yangit/flactyl/photos/1.jpeg

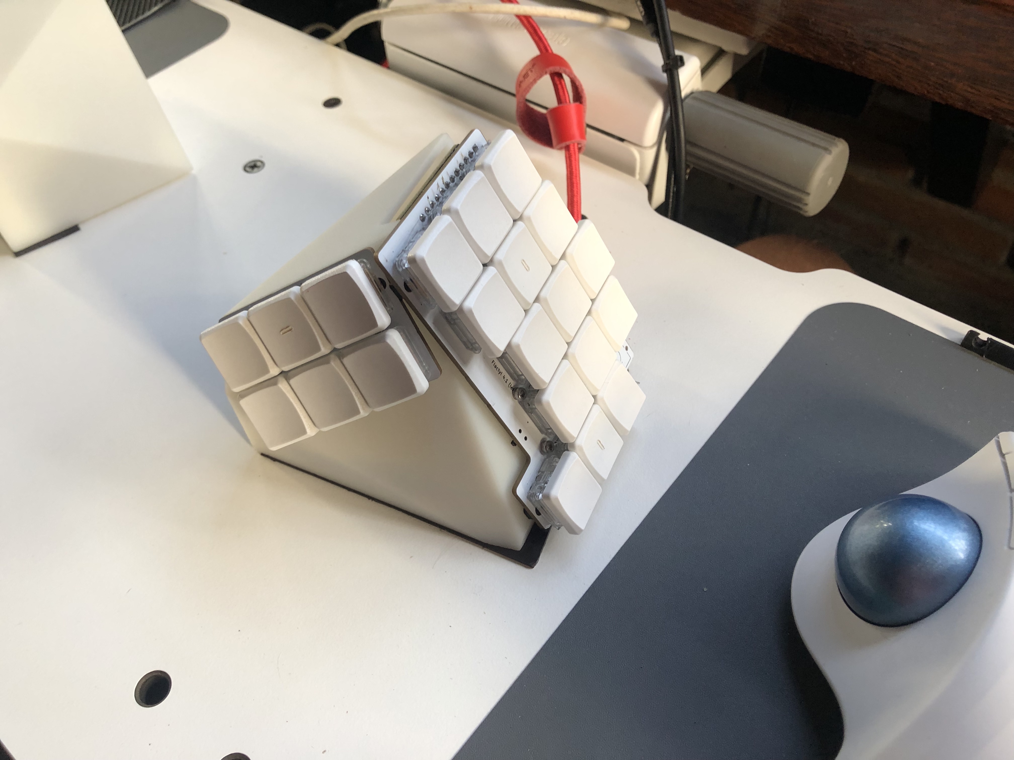
photos/1.jpeg
