yangit/flactyl/photos/4.jpeg

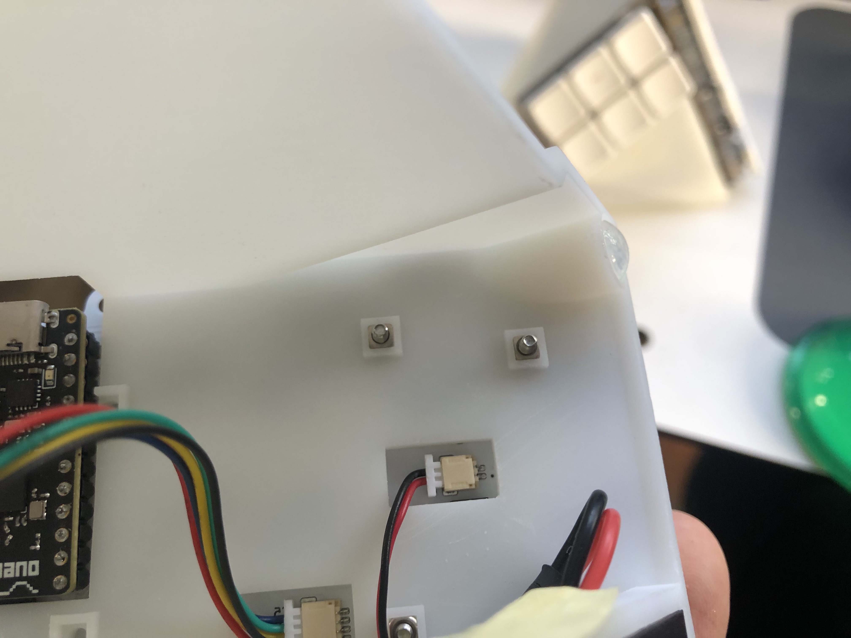
photos/4.jpeg
