yangit/flactyl/photos/6.jpeg

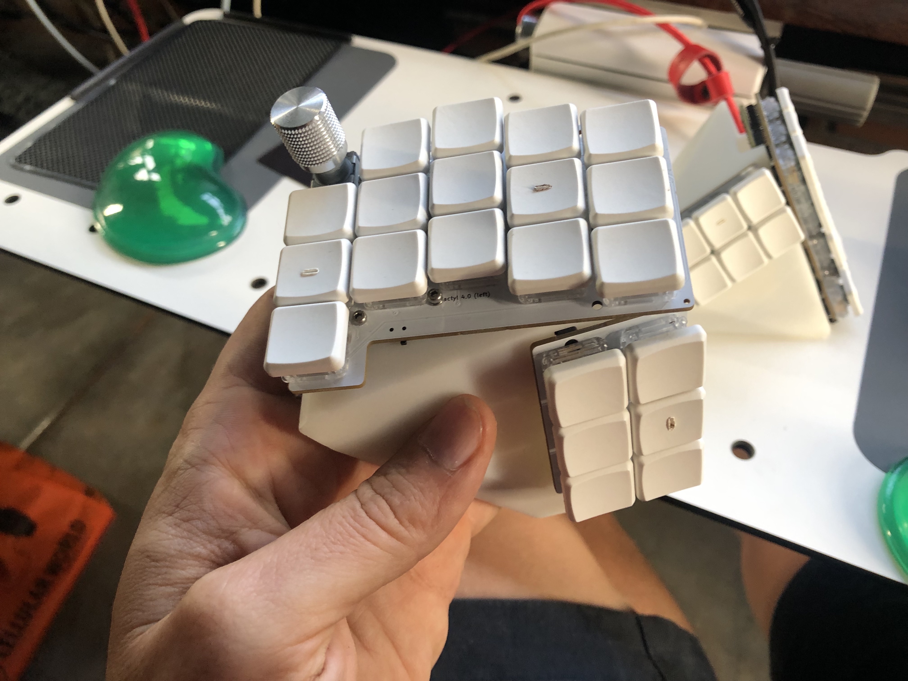
photos/6.jpeg
