yangit/flactyl/photos/7.jpeg

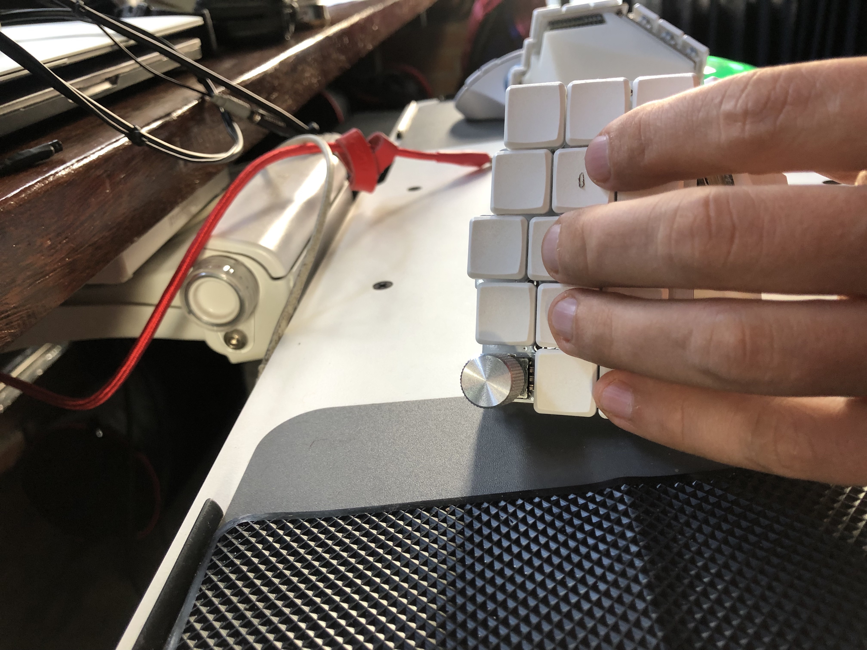
photos/7.jpeg
