yangit/flactyl/photos/8.jpeg

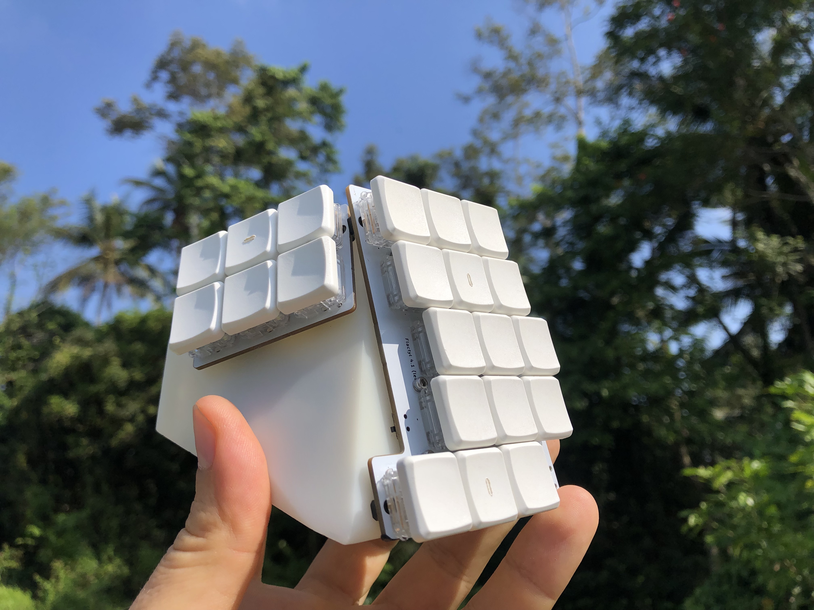
photos/8.jpeg
