yangit/flactyl/photos/9.jpeg

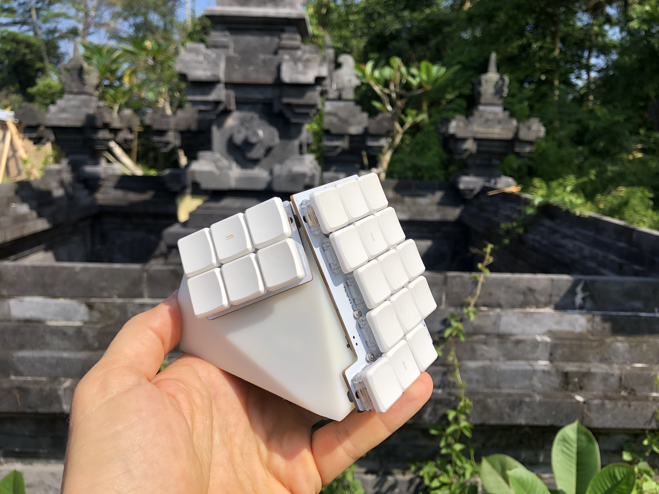
photos/9.jpeg
