yangit/flactyl/photos/10.jpeg

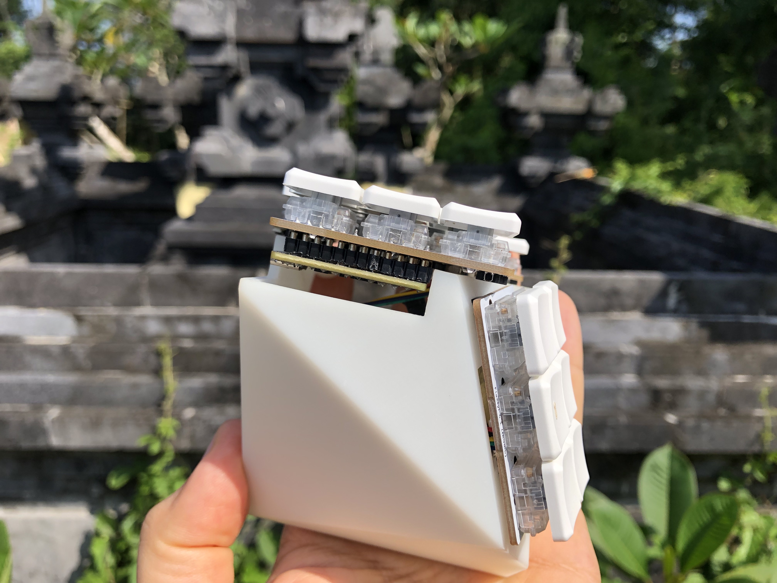
photos/10.jpeg
