yangit/flactyl/photos/11.jpeg

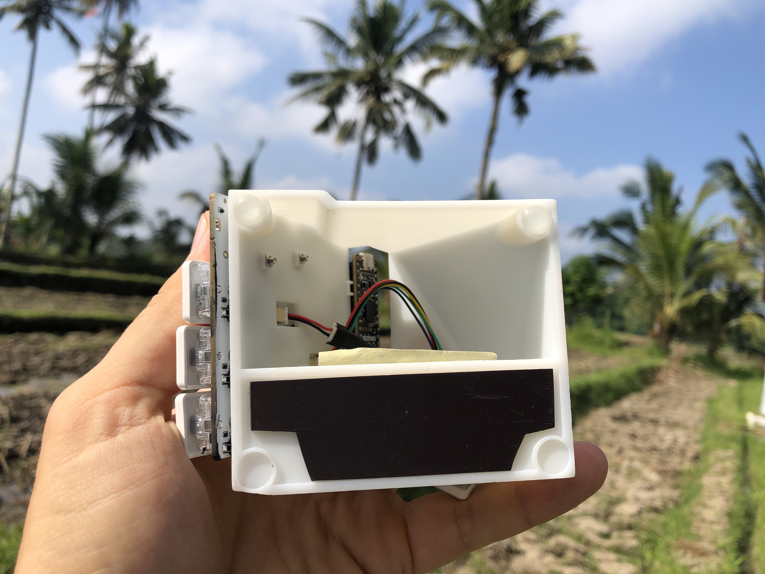
photos/11.jpeg
