yangit/flactyl/photos/12.jpeg

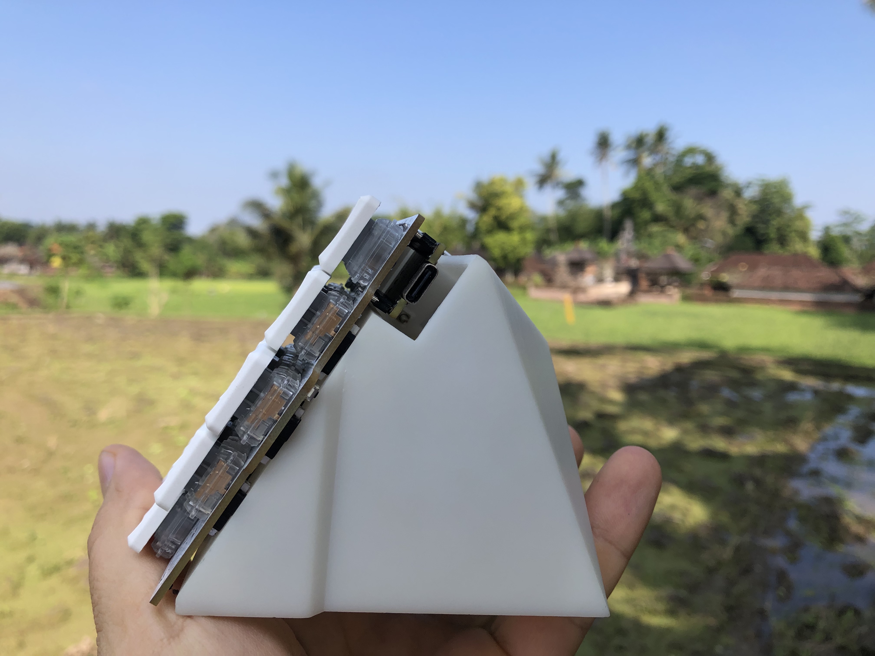
photos/12.jpeg
