yangit/flactyl/photos/cases/hitam1.png

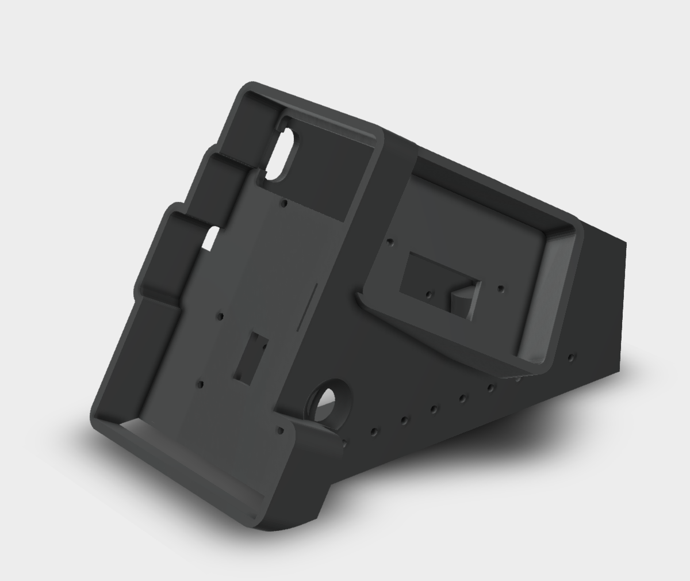
photos/cases/hitam1.png
