yangit/flactyl/photos/cases/hitam2.png

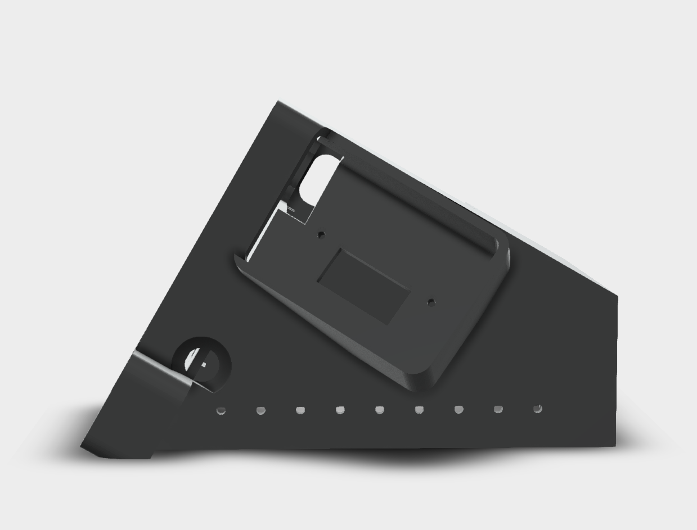
photos/cases/hitam2.png
