yangit/flactyl/production/case/4.2/iceberg/variant0/case4.png

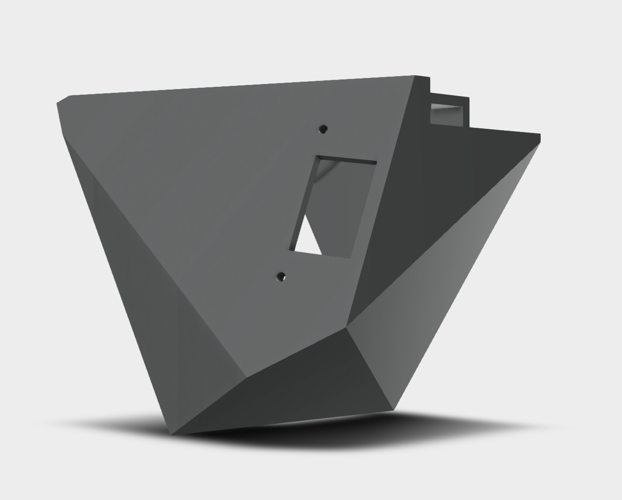
production/case/4.2/iceberg/variant0/case4.png
