yangit/flactyl/scad/4.2/clay/thumb.png

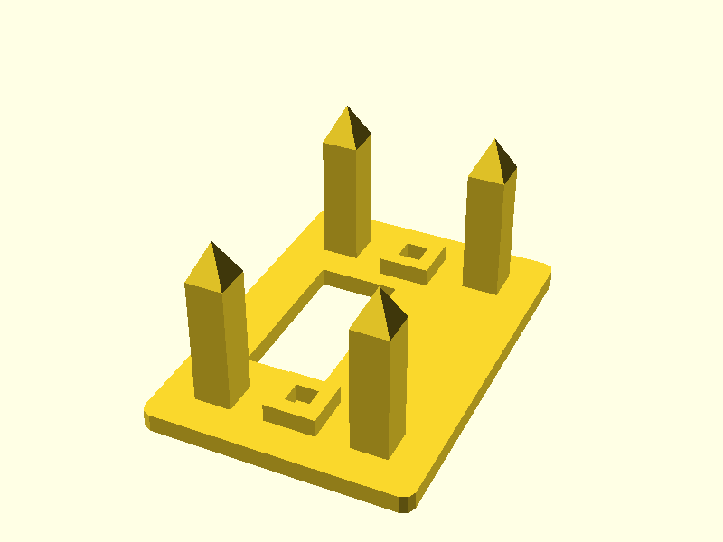
scad/4.2/clay/thumb.png
