yangit/flactyl/photos/parts/nut.webp

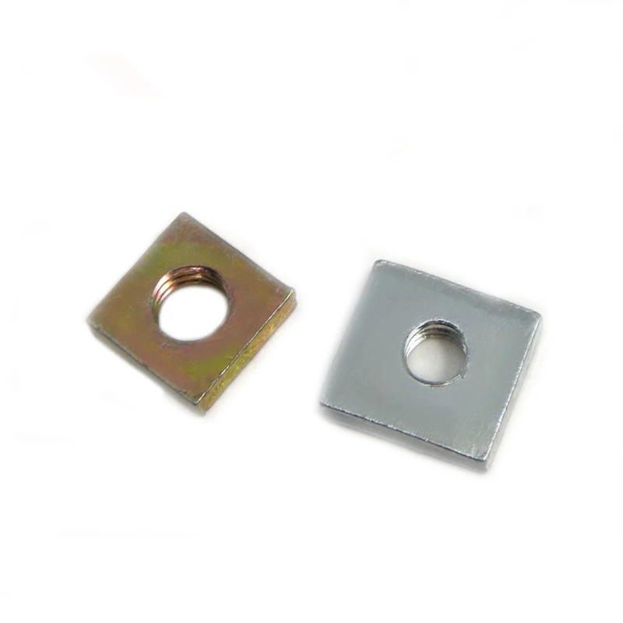
photos/parts/nut.webp
