yangit/flactyl/photos/parts/nut_how.jpg

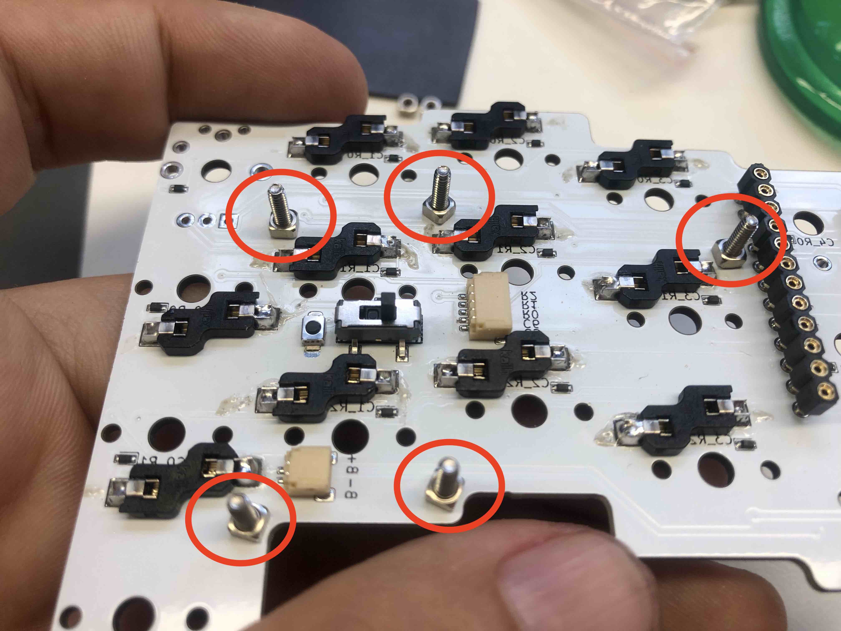
photos/parts/nut_how.jpg
