yangit/flactyl/production/case/iceberg/left2.stl

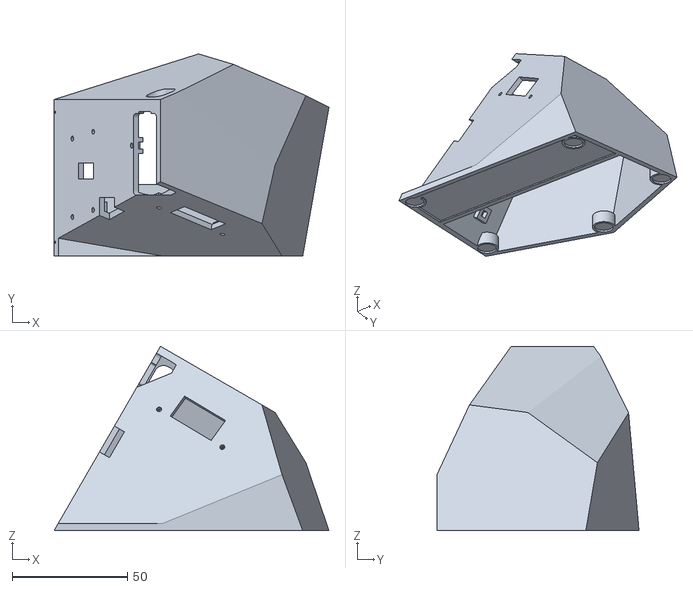
[picture p83: CAD file, 2023-06-13]
production/case/iceberg/left2.stl
119.5 x 87.8 x 80.1
