yangit/flactyl/production/manual_3d_print/batch0/case3 v20.stl

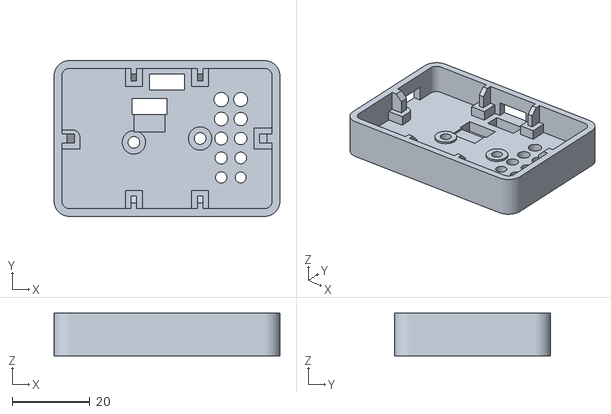
[picture p84: CAD file, 2023-05-24]
production/manual_3d_print/batch0/case3 v20.stl
58.0 x 40.0 x 11.0
