yangit/flactyl/production/manual_3d_print/batch1/switch_cutout_005.stl

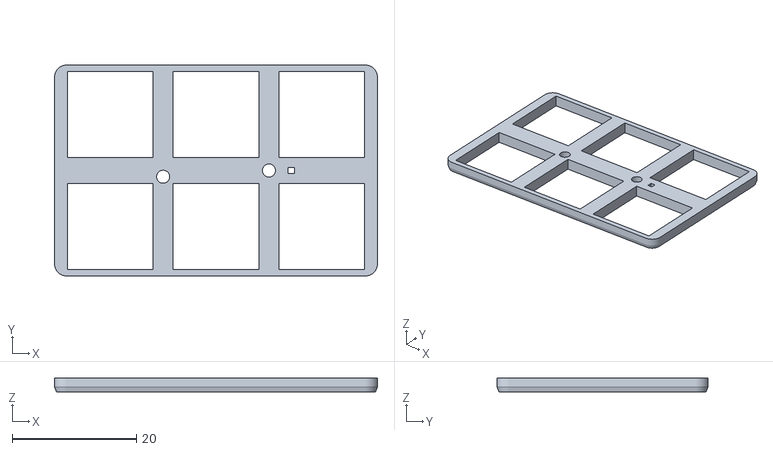
[picture p85: CAD file, 2023-05-24]
production/manual_3d_print/batch1/switch_cutout_005.stl
51.9 x 33.9 x 2.20
