yangit/flactyl/production/manual_3d_print/batch2/srcew-mount-bike.stl

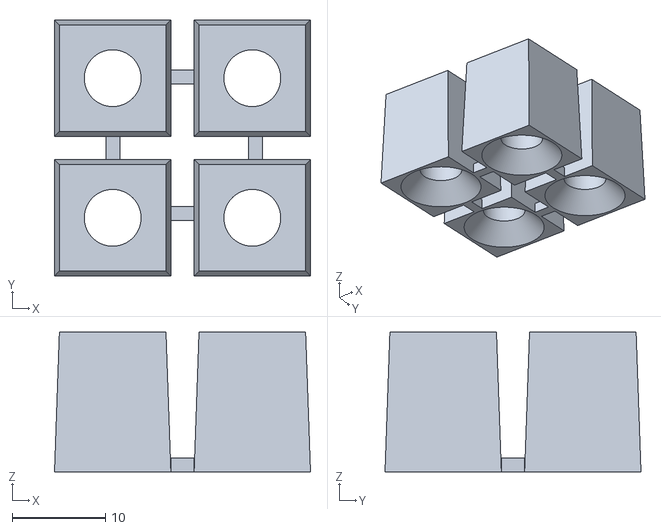
[picture p86: CAD file, 2023-05-24]
production/manual_3d_print/batch2/srcew-mount-bike.stl
27.5 x 27.5 x 15.0
