yangit/flactyl/production/manual_3d_print/batch3/left_3.2.stl

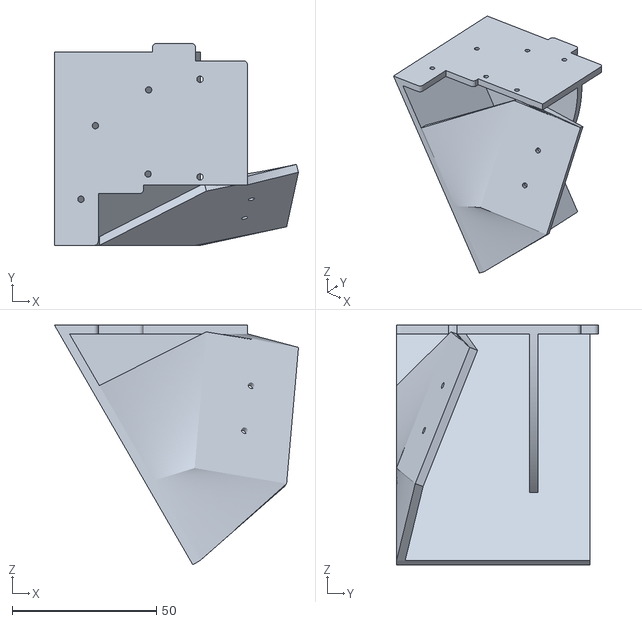
[picture p87: CAD file, 2023-05-24]
production/manual_3d_print/batch3/left_3.2.stl
84.6 x 70.0 x 83.0
