yangit/flactyl/production/pcbs/5.0/left/left.step

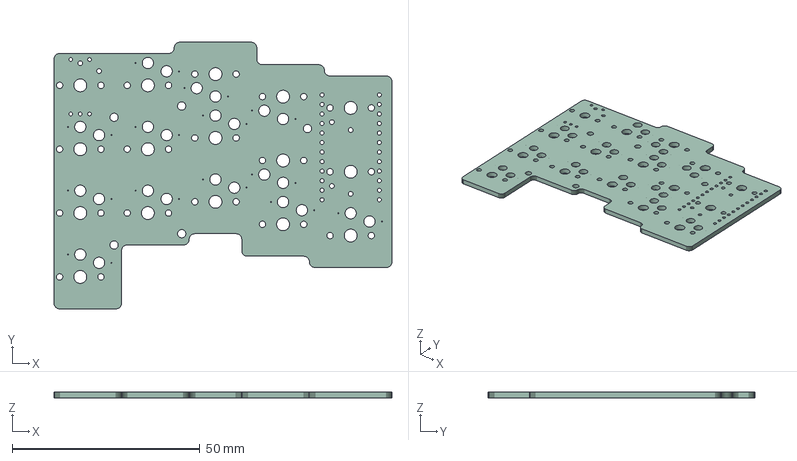
[picture p88: CAD file, 2023-06-15]
production/pcbs/5.0/left/left.step
90.0 x 71.0 x 1.60 mm
