yangit/flactyl/production/pcbs/5.0/thumb3/thumb3.step

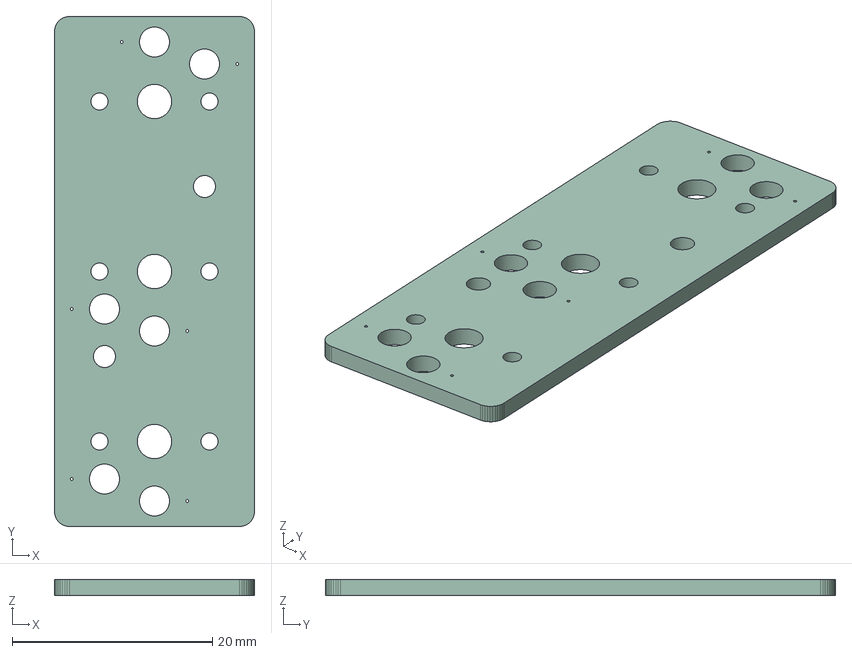
[picture p89: CAD file, 2023-06-29]
production/pcbs/5.0/thumb3/thumb3.step
20.0 x 51.0 x 1.60 mm
