yangit/flactyl/production/pcbs/5.1/test/test.step

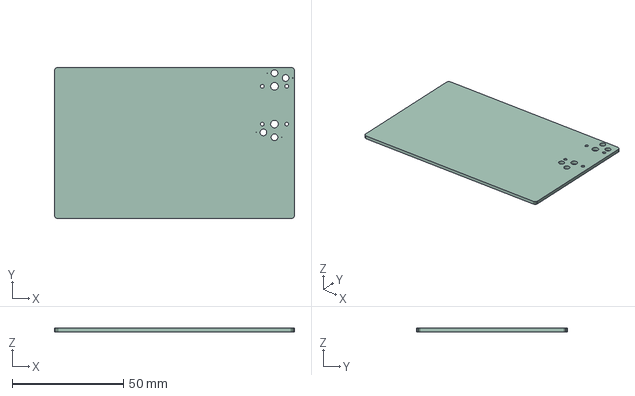
[picture p90: CAD file, 2023-08-01]
production/pcbs/5.1/test/test.step
108.0 x 68.0 x 1.60 mm
