yangit/flactyl/production/pcbs/5.1/thumb/thumb.step

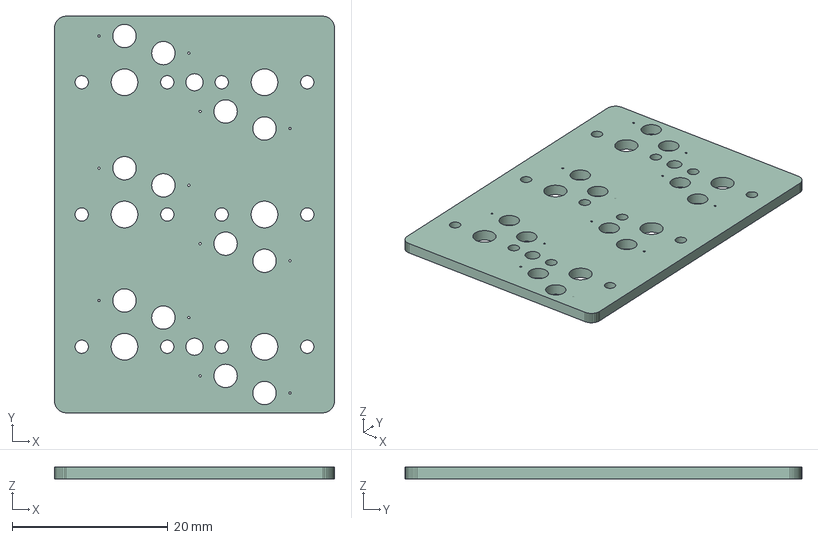
[picture p91: CAD file, 2023-08-01]
production/pcbs/5.1/thumb/thumb.step
36.0 x 51.0 x 1.60 mm
