yangit/flactyl/scad/4.2/shared-3d-models/nice-nano.step

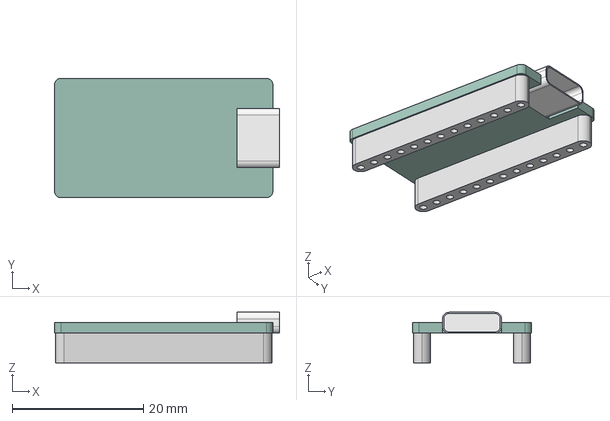
[picture p92: CAD file, 2023-06-29]
scad/4.2/shared-3d-models/nice-nano.step
34.3 x 18.2 x 7.70 mm
