yangit/flactyl/scad/5.0/shared-3d-models/pg1350_socket.3mf

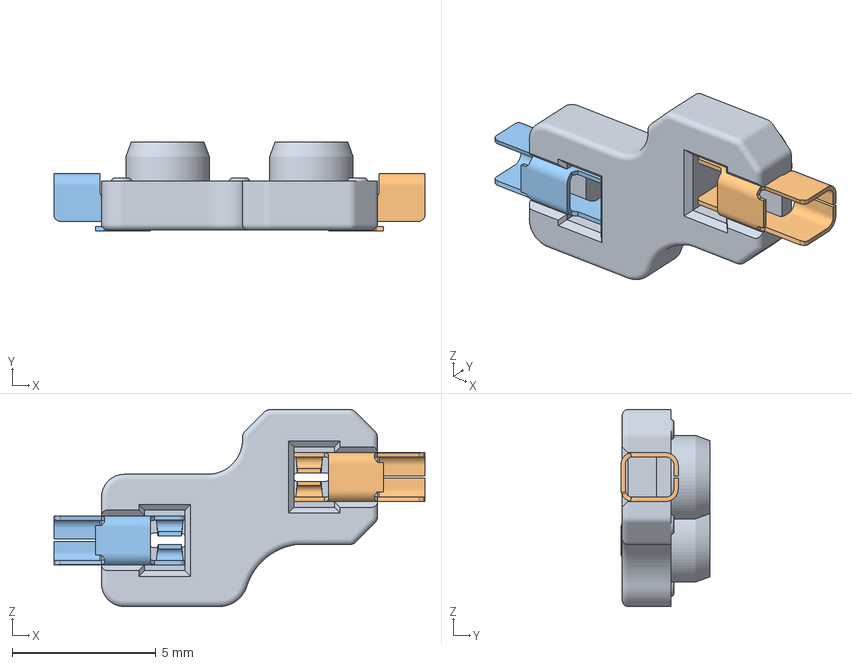
[picture p93: CAD file, 2023-07-01]
scad/5.0/shared-3d-models/pg1350_socket.3mf
12.9 x 3.09 x 6.85 mm
