yangit/flactyl/scad/5.0/shared-3d-models/ploopy-nano/STEPs/RollerBearingDowel.stp

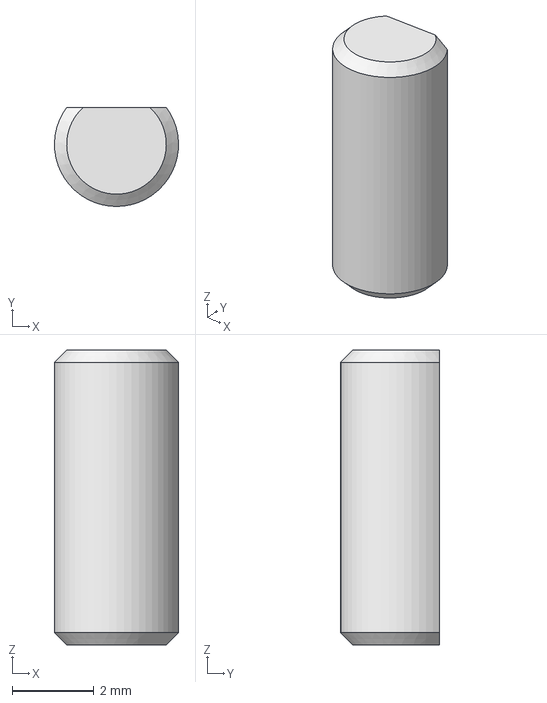
[picture p94: CAD file, 2023-06-29]
scad/5.0/shared-3d-models/ploopy-nano/STEPs/RollerBearingDowel.stp
3.03 x 2.42 x 7.20 mm
