yangit/flactyl/scad/5.0/shared-3d-models/ploopy-nano/STLs/Kit Bearing Press Bottom.stl

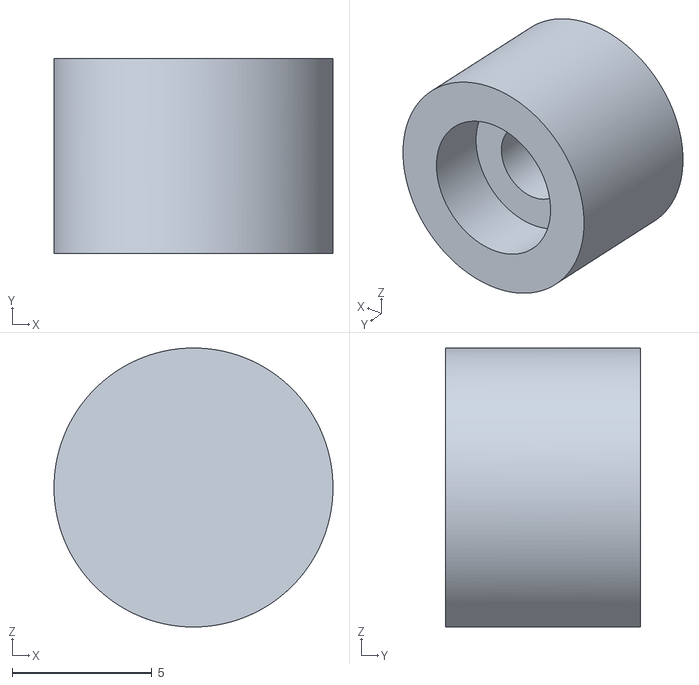
[picture p95: CAD file, 2023-06-29]
scad/5.0/shared-3d-models/ploopy-nano/STLs/Kit Bearing Press Bottom.stl
10.00 x 7.00 x 10.00
