yangit/flactyl/case/external_models/acrylic.dxf

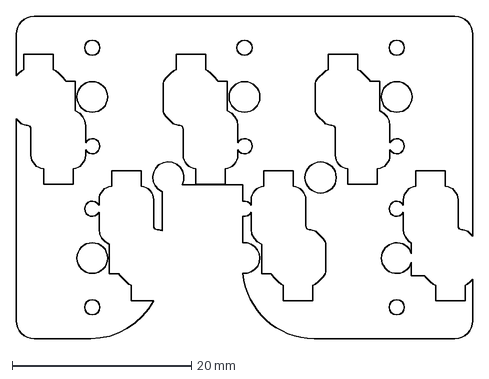
[picture p96: CAD file, 2023-05-24]
case/external_models/acrylic.dxf
51.0 x 36.0 mm
