yangit/flactyl/production/4.0/test/test.step

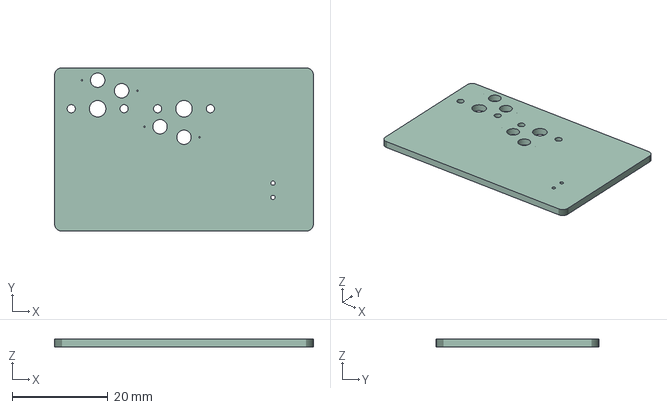
[picture p97: CAD file, 2023-06-08]
production/4.0/test/test.step
54.0 x 34.0 x 1.60 mm
