yangit/flactyl/production/4.1/right/right_keycaps.dxf

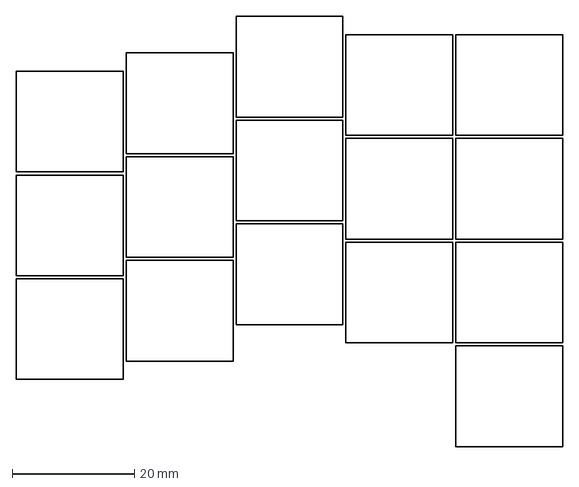
[picture p98: CAD file, 2023-06-08]
production/4.1/right/right_keycaps.dxf
89.5 x 70.5 mm
