yangit/flactyl/production/4.1/thumb/thumb_keycaps.dxf

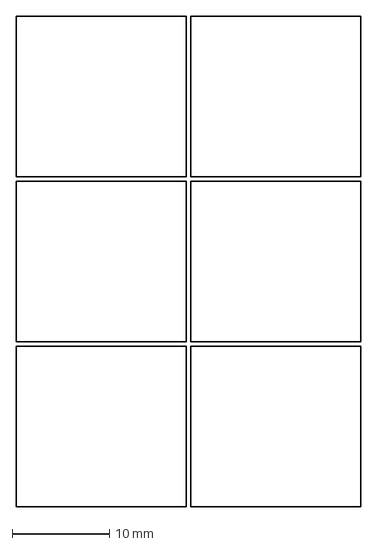
[picture p99: CAD file, 2023-06-08]
production/4.1/thumb/thumb_keycaps.dxf
35.5 x 50.5 mm
