yangit/flactyl/production/case/4.2/iceberg/variant0/right.stl

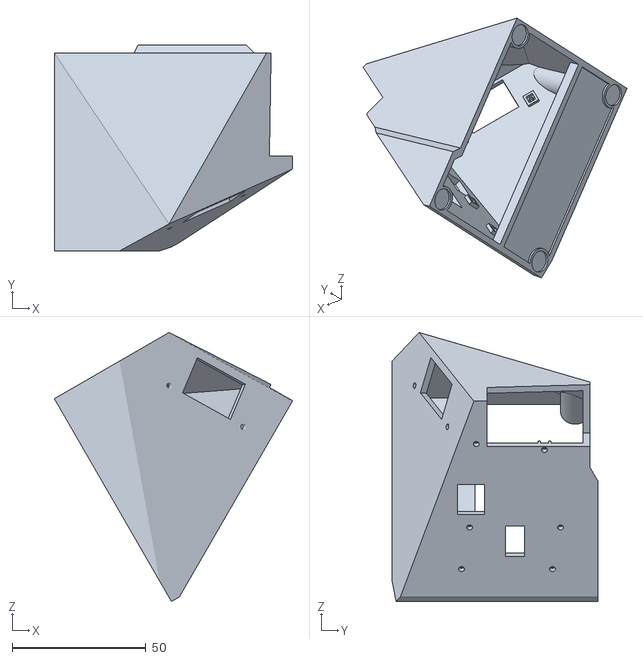
[picture p100: CAD file, 2023-05-24]
production/case/4.2/iceberg/variant0/right.stl
89.1 x 77.0 x 100.6
