yangit/flactyl/production/case/5.0/clay/thumb.stl

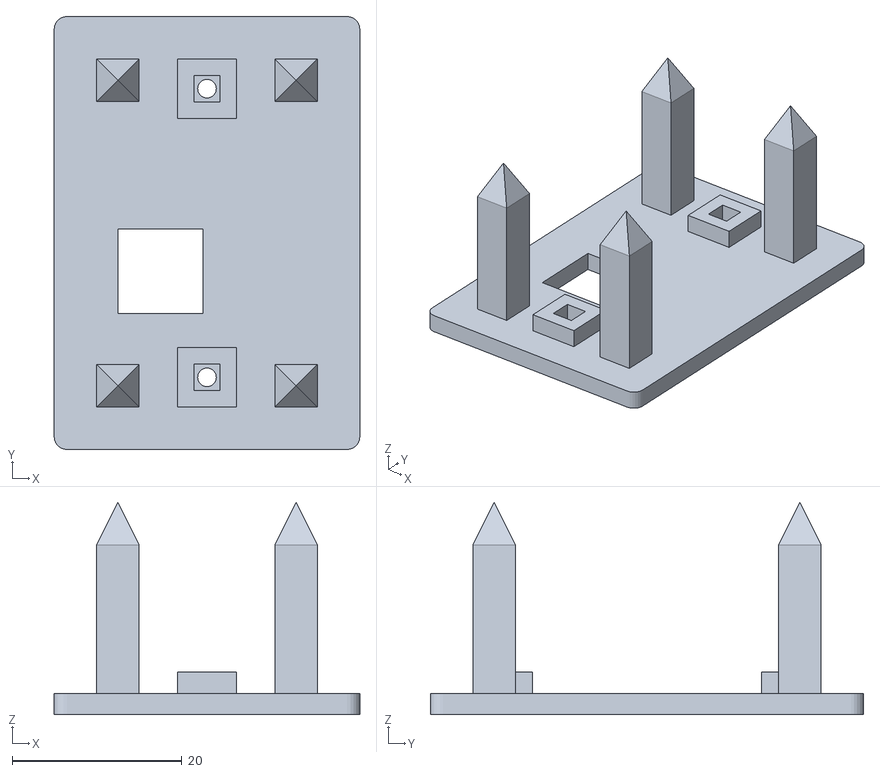
[picture p101: CAD file, 2023-07-02]
production/case/5.0/clay/thumb.stl
36.0 x 51.0 x 25.0
