yangit/flactyl/production/manual_3d_print/batch0/Holder v18_narrow.stl

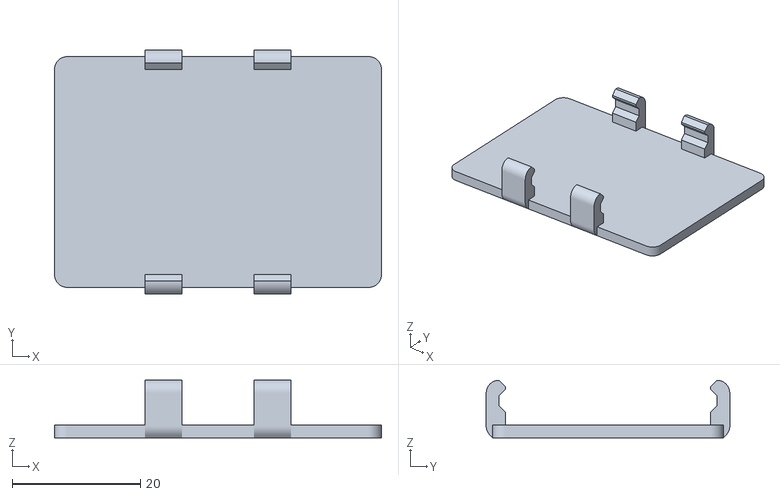
[picture p102: CAD file, 2023-05-24]
production/manual_3d_print/batch0/Holder v18_narrow.stl
51.0 x 38.0 x 8.97
