yangit/flactyl/production/manual_3d_print/batch1/switch_cutout_030.stl

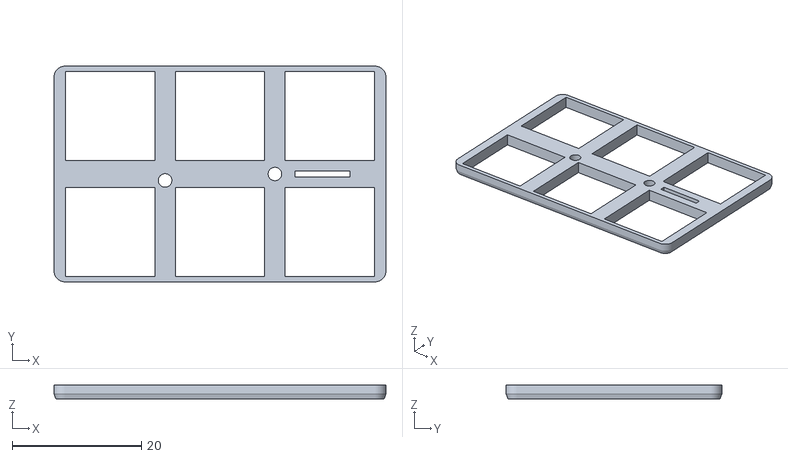
[picture p103: CAD file, 2023-05-24]
production/manual_3d_print/batch1/switch_cutout_030.stl
51.4 x 33.4 x 2.20
