yangit/flactyl/production/manual_3d_print/batch2/trainKaki.stl

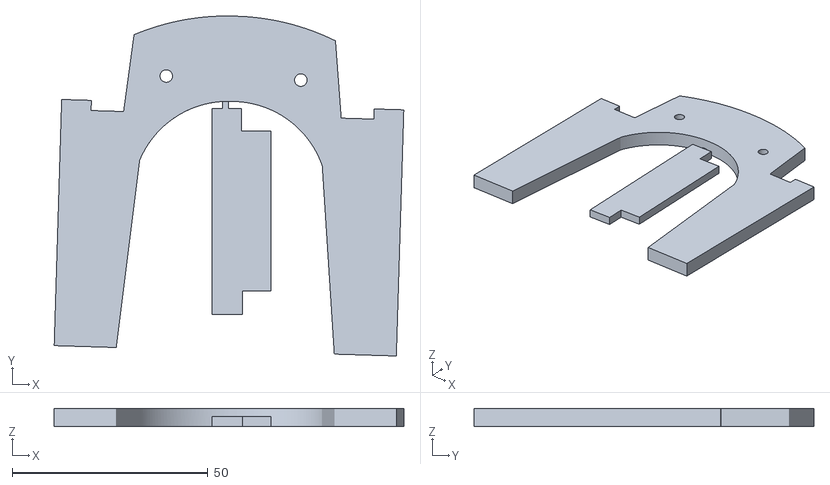
[picture p104: CAD file, 2023-05-24]
production/manual_3d_print/batch2/trainKaki.stl
89.3 x 86.8 x 4.60
