yangit/flactyl/production/manual_3d_print/batch3/right_3.2.stl

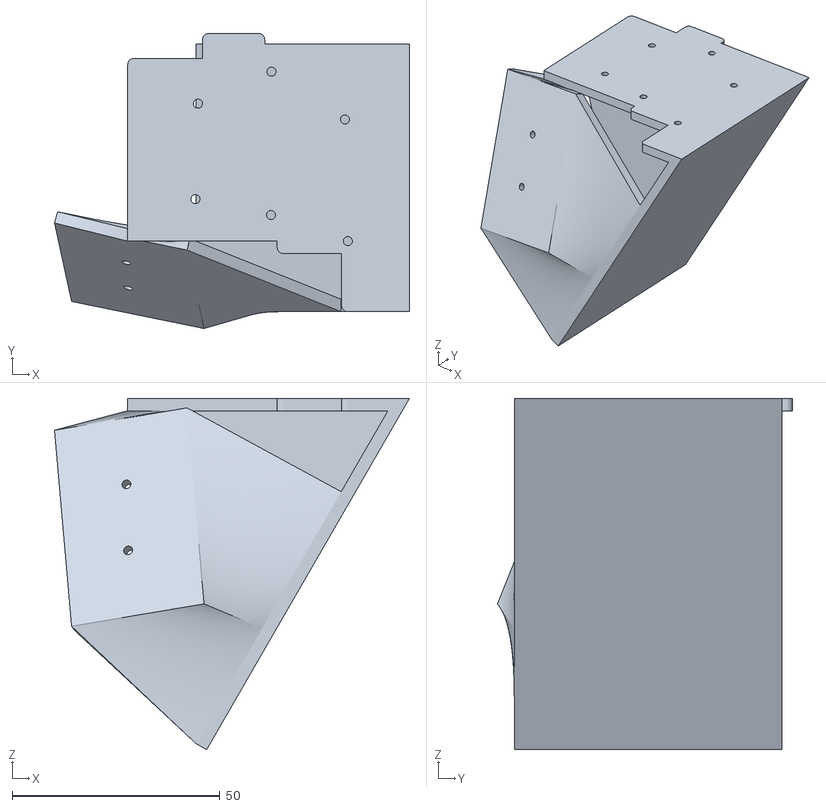
[picture p105: CAD file, 2023-05-24]
production/manual_3d_print/batch3/right_3.2.stl
85.5 x 71.0 x 84.6
