yangit/flactyl/production/pcbs/5.1/left/left_pcb_edgecut.dxf

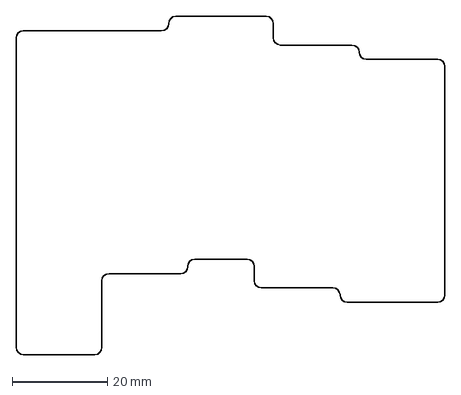
[picture p106: CAD file, 2023-06-15]
production/pcbs/5.1/left/left_pcb_edgecut.dxf
90.0 x 71.0 mm
