yangit/flactyl/production/pcbs/5.1/test/test_keycaps.dxf

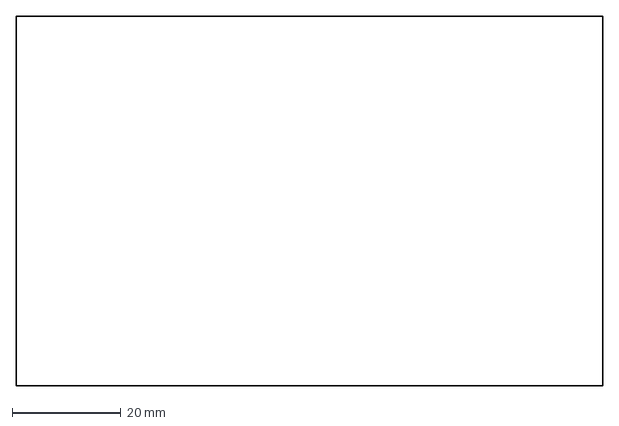
[picture p107: CAD file, 2023-06-08]
production/pcbs/5.1/test/test_keycaps.dxf
108.0 x 68.0 mm
