yangit/flactyl/production/pcbs/5.1/thumb/thumb_case.dxf

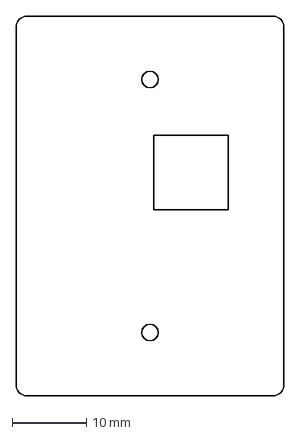
[picture p108: CAD file, 2023-08-01]
production/pcbs/5.1/thumb/thumb_case.dxf
36.0 x 51.0 mm
