yangit/flactyl/scad/4.2/shared-3d-models/choc-hot.stl

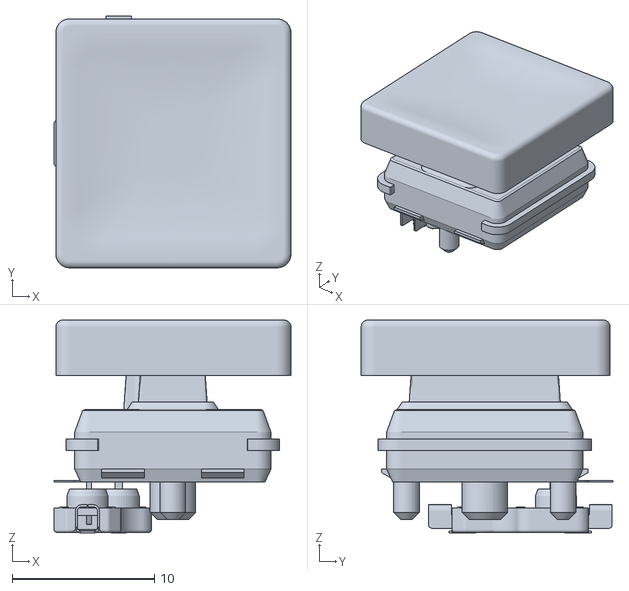
[picture p109: CAD file, 2023-06-01]
scad/4.2/shared-3d-models/choc-hot.stl
16.7 x 17.7 x 15.0
