yangit/flactyl/scad/5.0/shared-3d-models/ploopy-nano/STLs/Kit Bearing Press Top.stl

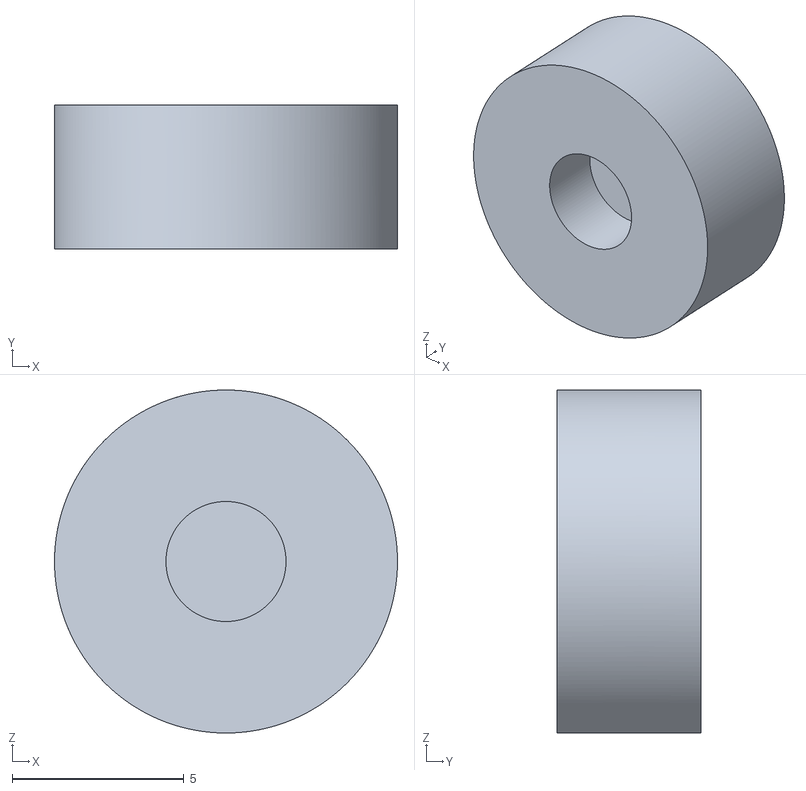
[picture p110: CAD file, 2023-06-29]
scad/5.0/shared-3d-models/ploopy-nano/STLs/Kit Bearing Press Top.stl
10.00 x 4.20 x 10.00
