yangit/flactyl/case/external_models/Kailh LP Choc PC Keycap.step

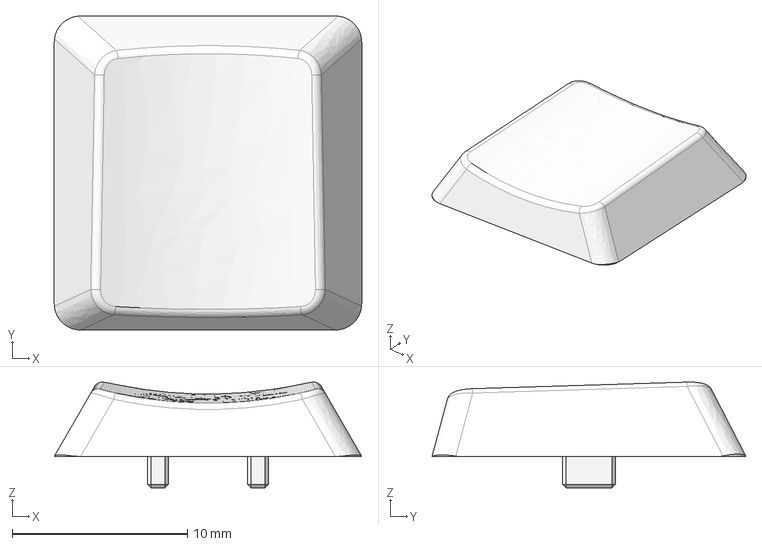
[picture p111: CAD file, 2023-05-24]
case/external_models/Kailh LP Choc PC Keycap.step
17.5 x 17.9 x 6.03 mm
