yangit/flactyl/production/4.0/test/test_pcb_edgecut.dxf

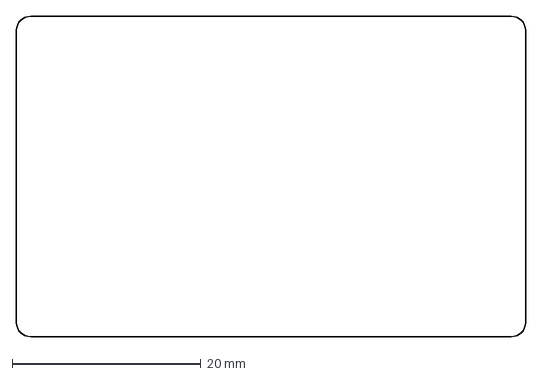
[picture p112: CAD file, 2023-06-08]
production/4.0/test/test_pcb_edgecut.dxf
54.0 x 34.0 mm
