yangit/flactyl/production/case/4.2/clay/thumb.stl

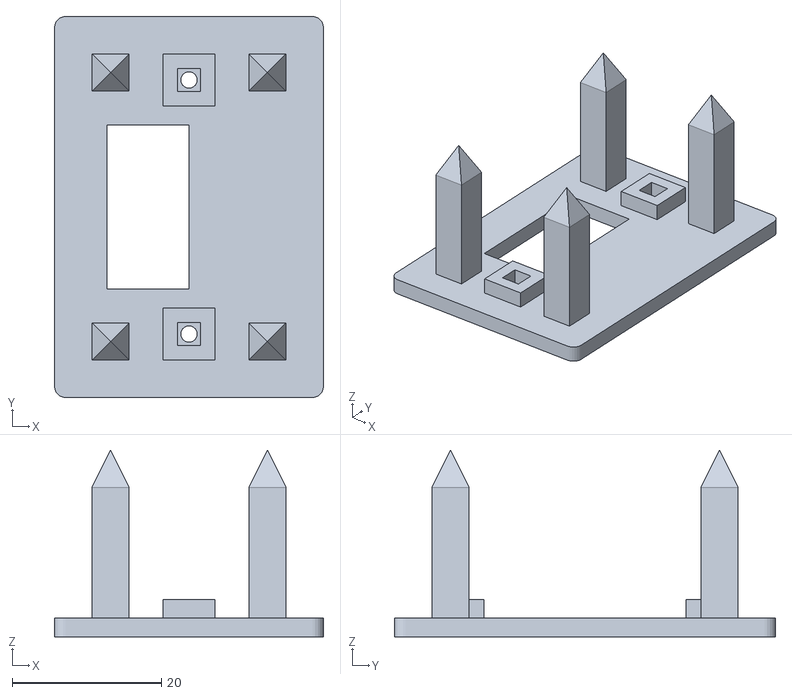
[picture p113: CAD file, 2023-06-13]
production/case/4.2/clay/thumb.stl
36.0 x 51.0 x 25.0
