yangit/flactyl/production/manual_3d_print/batch2/srcew-mount-bike-single.stl

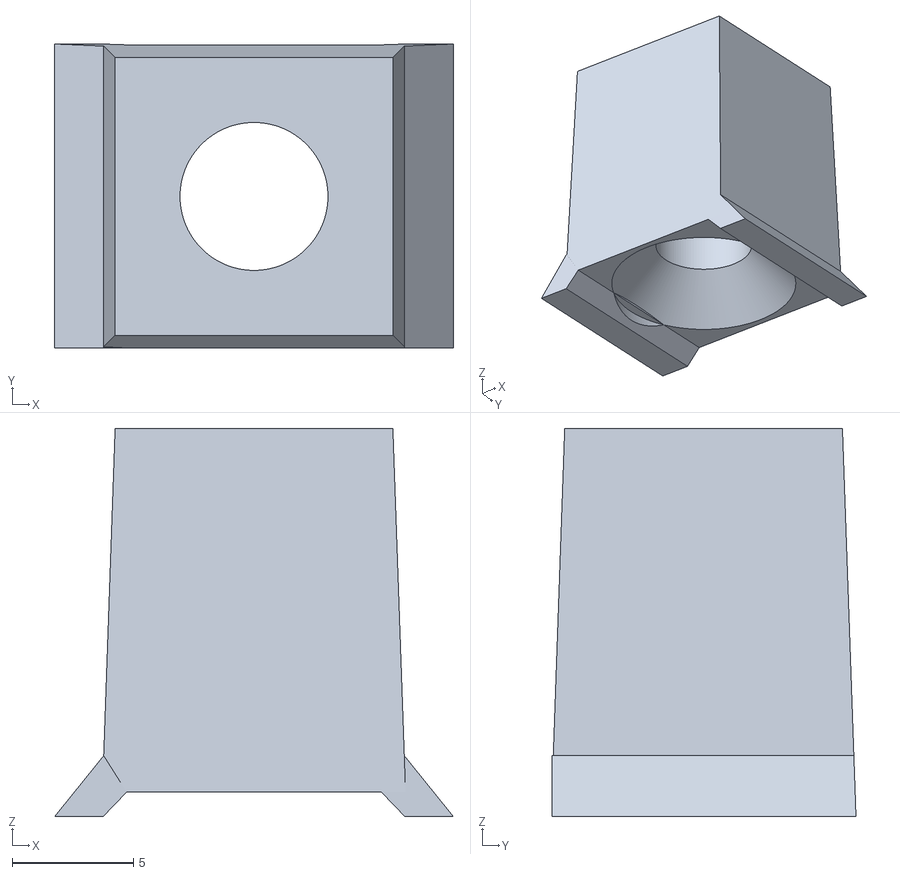
[picture p114: CAD file, 2023-05-24]
production/manual_3d_print/batch2/srcew-mount-bike-single.stl
16.5 x 12.5 x 16.0
