yangit/flactyl/production/pcbs/5.1/thumb3/thumb3_case.dxf

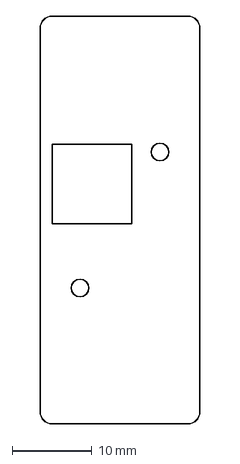
[picture p117: CAD file, 2023-06-29]
production/pcbs/5.1/thumb3/thumb3_case.dxf
20.0 x 51.0 mm
