yangit/flactyl/scad/5.0/shared-3d-models/choc_keycap.3mf

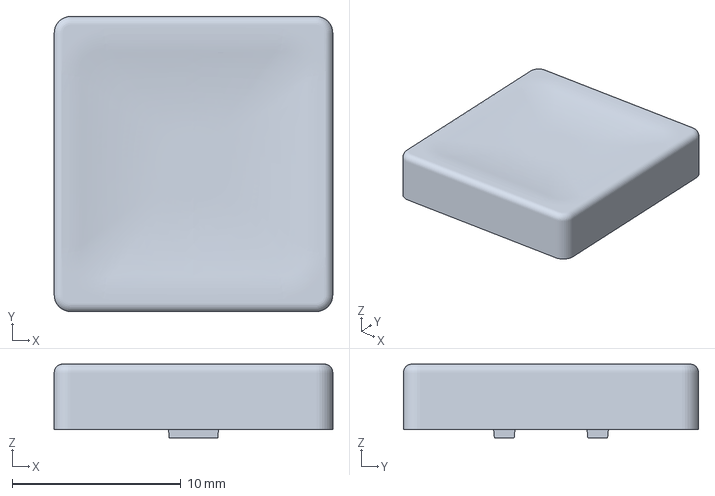
[picture p118: CAD file, 2023-07-01]
scad/5.0/shared-3d-models/choc_keycap.3mf
16.5 x 17.5 x 4.38 mm
