yangit/flactyl/scad/5.0/shared-3d-models/ploopy-nano/STEPs/Bottom.step

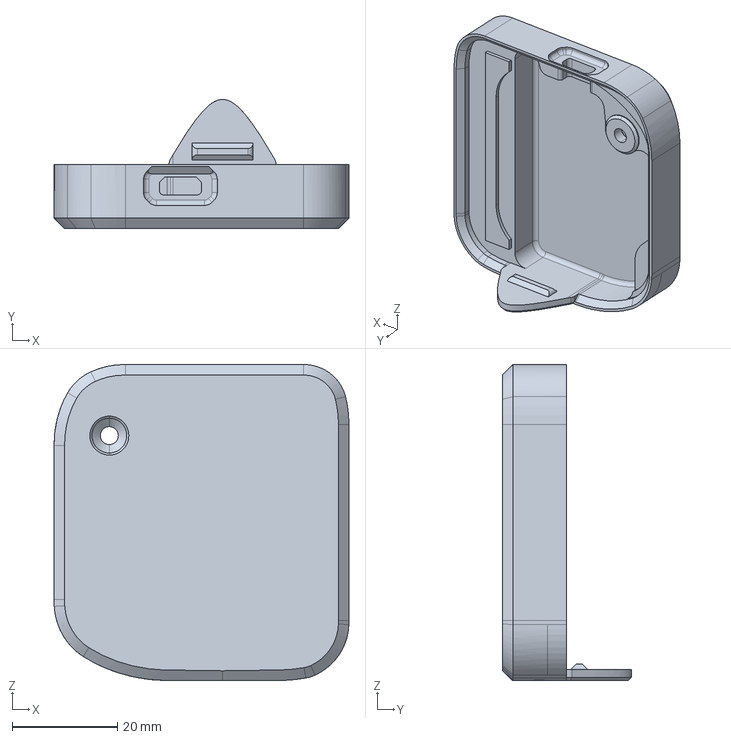
[picture p119: CAD file, 2023-06-29]
scad/5.0/shared-3d-models/ploopy-nano/STEPs/Bottom.step
56.0 x 24.5 x 60.0 mm
