yangit/flactyl/case/external_models/PG1350-socket.STEP

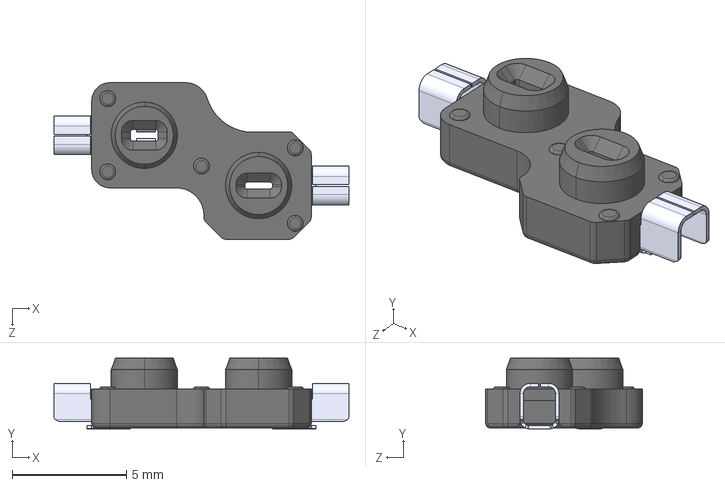
[picture p120: CAD file, 2023-05-24]
case/external_models/PG1350-socket.STEP
12.9 x 3.09 x 6.85 mm
pin x 2
socket
