yangit/flactyl/production/4.0/test/test_keycaps.dxf

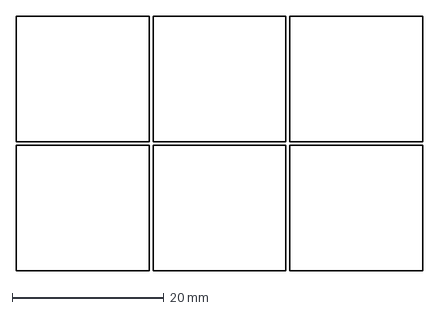
[picture p121: CAD file, 2023-06-08]
production/4.0/test/test_keycaps.dxf
53.5 x 33.5 mm
