yangit/flactyl/production/manual_3d_print/batch1/tester_holes.stl

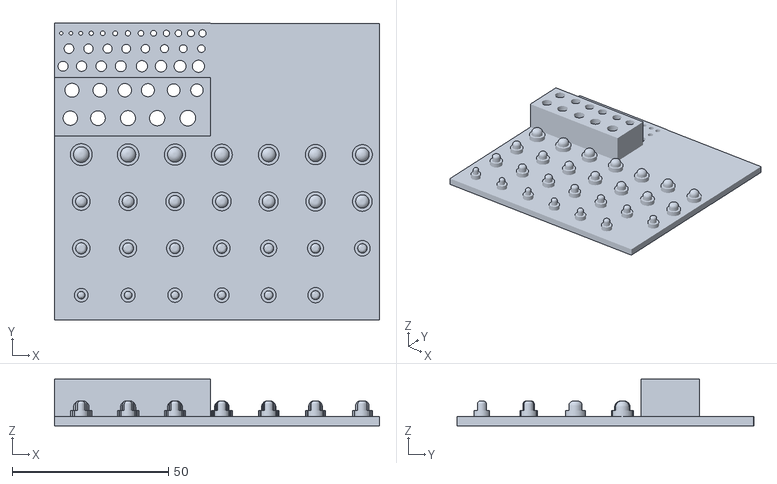
[picture p122: CAD file, 2023-05-24]
production/manual_3d_print/batch1/tester_holes.stl
104.1 x 95.2 x 15.0
