yangit/flactyl/production/pcbs/5.1/left/left_case_nano.dxf

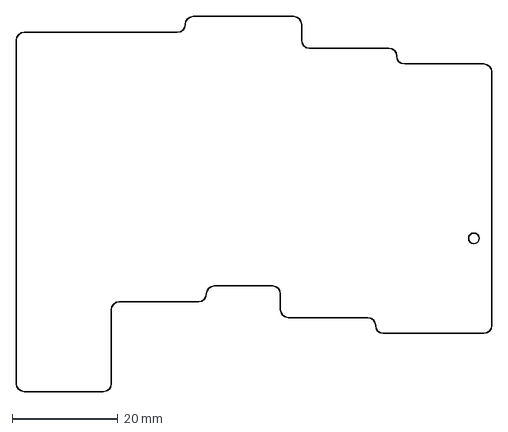
[picture p123: CAD file, 2023-06-15]
production/pcbs/5.1/left/left_case_nano.dxf
90.0 x 71.0 mm
