yangit/flactyl/production/pcbs/5.1/right/right_case_nano.dxf

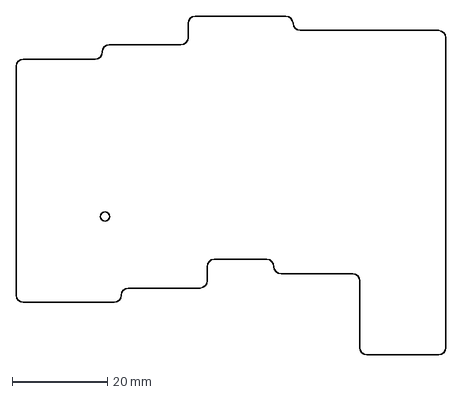
[picture p124: CAD file, 2023-06-15]
production/pcbs/5.1/right/right_case_nano.dxf
90.0 x 71.0 mm
