yangit/flactyl/production/pcbs/5.1/test/test_pcb_edgecut.dxf

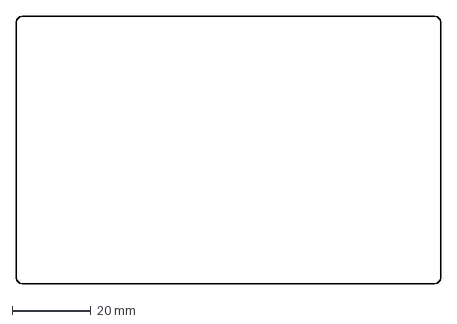
[picture p125: CAD file, 2023-06-08]
production/pcbs/5.1/test/test_pcb_edgecut.dxf
108.0 x 68.0 mm
