yangit/flactyl/production/pcbs/5.1/thumb/thumb_keycaps_round.dxf

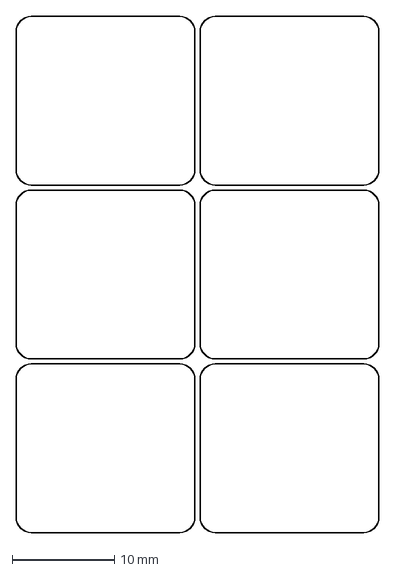
[picture p126: CAD file, 2023-06-13]
production/pcbs/5.1/thumb/thumb_keycaps_round.dxf
35.5 x 50.5 mm
