yangit/flactyl/production/pcbs/5.1/thumb3/thumb3_keycaps_round.dxf

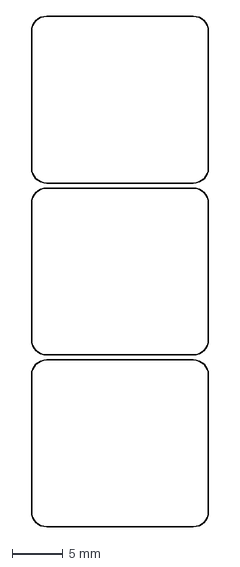
[picture p127: CAD file, 2023-06-29]
production/pcbs/5.1/thumb3/thumb3_keycaps_round.dxf
17.5 x 50.5 mm
