yangit/flactyl/scad/5.0/shared-3d-models/ploopy-nano/STEPs/PCB.step

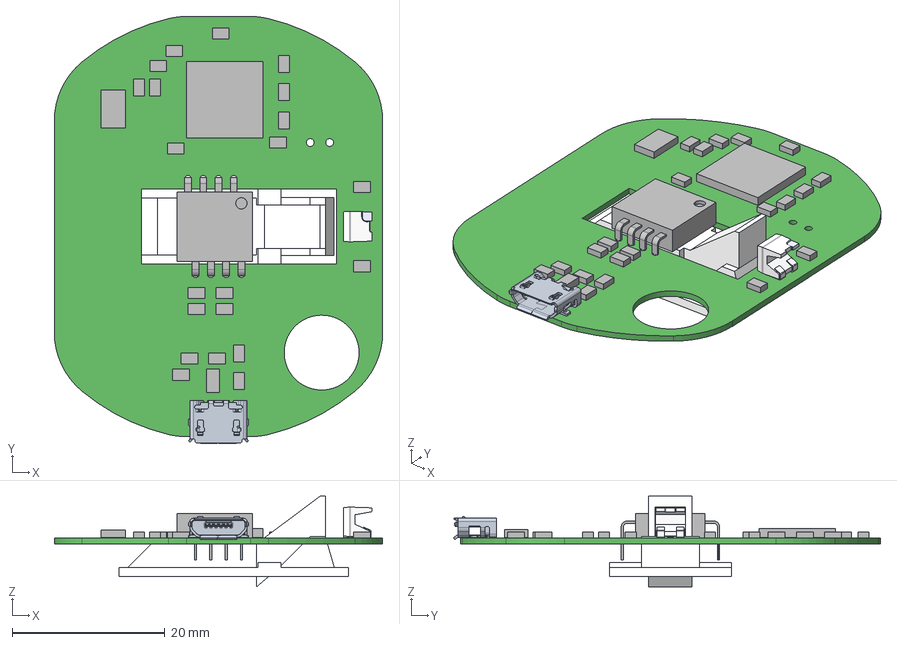
[picture p128: CAD file, 2023-06-29]
scad/5.0/shared-3d-models/ploopy-nano/STEPs/PCB.step
43.0 x 55.9 x 11.8 mm
Extruded x 24
10118192C
ADNS-5050
ADNS-5050-Optic
LS_A67F_20091130_geometry_RGB15987699 x 3
