yangit/flactyl/production/manual_3d_print/batch0/Holder v13.stl

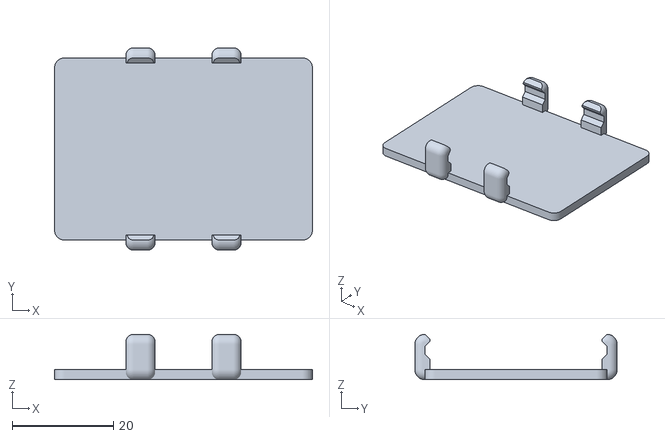
[picture p130: CAD file, 2023-05-24]
production/manual_3d_print/batch0/Holder v13.stl
51.0 x 40.0 x 8.97
