yangit/flactyl/production/pcbs/5.1/right/right_keycaps_round.dxf

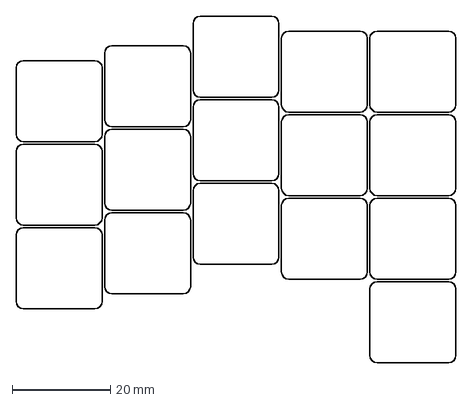
[picture p132: CAD file, 2023-06-15]
production/pcbs/5.1/right/right_keycaps_round.dxf
89.5 x 70.5 mm
