yangit/flactyl/production/pcbs/5.1/test/test_switch_cutouts.dxf

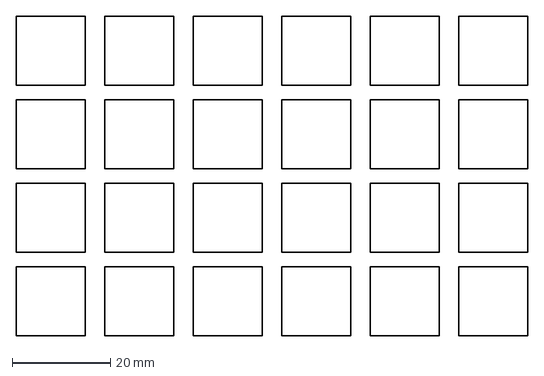
[picture p133: CAD file, 2023-06-08]
production/pcbs/5.1/test/test_switch_cutouts.dxf
104.0 x 65.0 mm
