yangit/flactyl/production/manual_3d_print/batch0/Holder v19_wide_0.0.stl

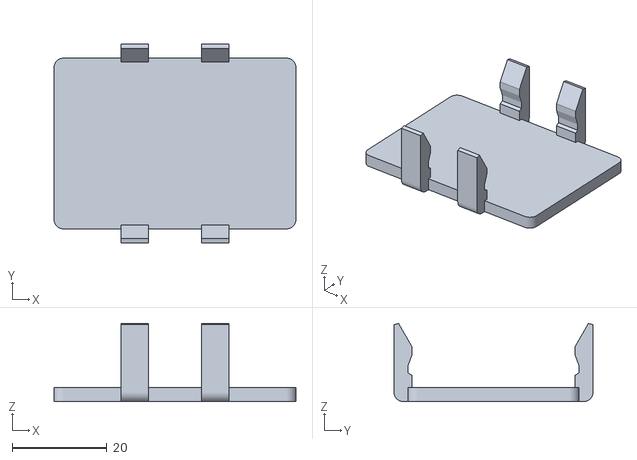
[picture p134: CAD file, 2023-05-24]
production/manual_3d_print/batch0/Holder v19_wide_0.0.stl
51.0 x 42.0 x 16.4
