yangit/flactyl/production/pcbs/5.1/left/left_case.dxf

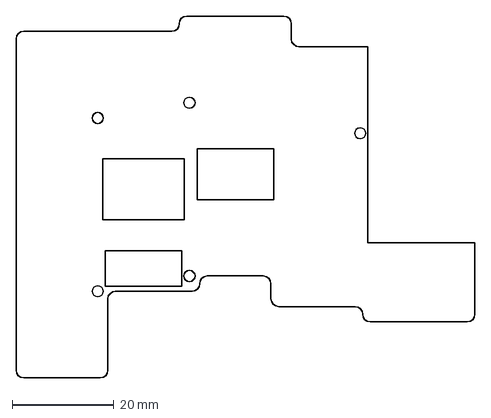
[picture p135: CAD file, 2023-06-15]
production/pcbs/5.1/left/left_case.dxf
90.0 x 71.0 mm
