yangit/flactyl/production/pcbs/5.1/thumb/thumb_keycaps.dxf

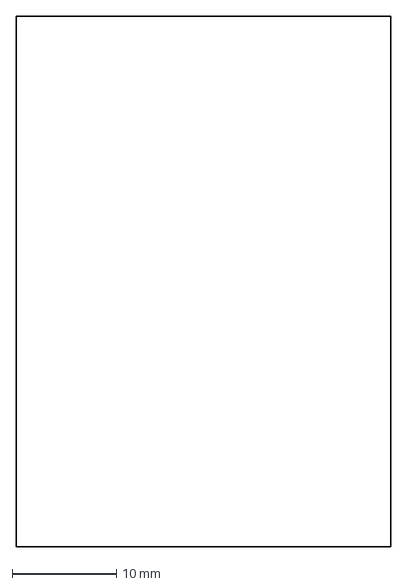
[picture p137: CAD file, 2023-06-08]
production/pcbs/5.1/thumb/thumb_keycaps.dxf
36.0 x 51.0 mm
