yangit/flactyl/production/pcbs/5.1/thumb3/thumb3_keycaps.dxf

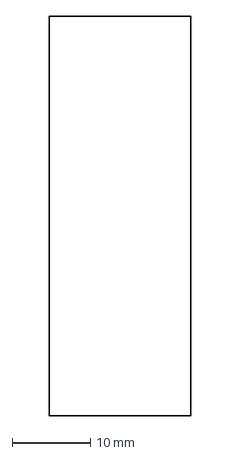
[picture p138: CAD file, 2023-06-29]
production/pcbs/5.1/thumb3/thumb3_keycaps.dxf
18.0 x 51.0 mm
