yangit/flactyl/production/pcbs/5.1/left/left_keycaps_round.dxf

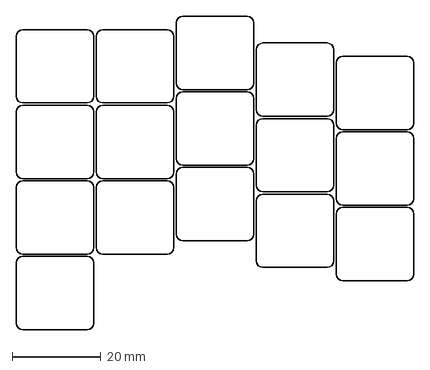
[picture p139: CAD file, 2023-06-13]
production/pcbs/5.1/left/left_keycaps_round.dxf
89.5 x 70.5 mm
