yangit/flactyl/production/pcbs/5.1/right/right_pcb_edgecut_with_keys.dxf

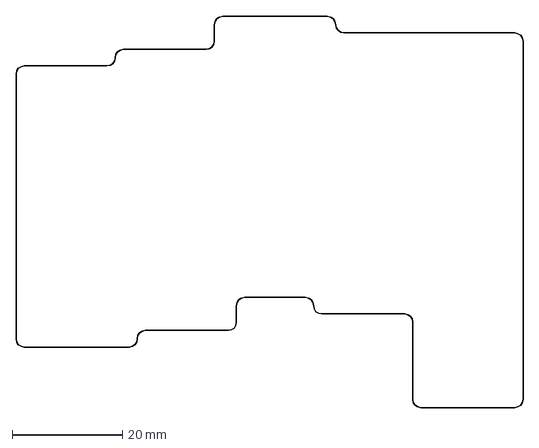
[picture p140: CAD file, 2023-06-15]
production/pcbs/5.1/right/right_pcb_edgecut_with_keys.dxf
92.0 x 71.0 mm
