yangit/flactyl/production/pcbs/5.1/thumb/thumb_switch_cutouts.dxf

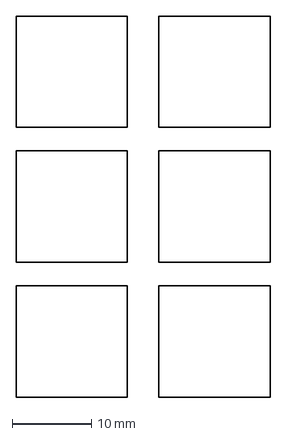
[picture p141: CAD file, 2023-06-08]
production/pcbs/5.1/thumb/thumb_switch_cutouts.dxf
32.0 x 48.0 mm
