yangit/flactyl/production/pcbs/5.1/thumb3/thumb3_switch_cutouts.dxf

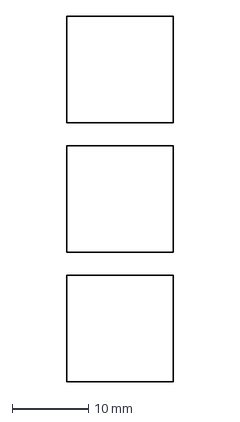
[picture p142: CAD file, 2023-06-29]
production/pcbs/5.1/thumb3/thumb3_switch_cutouts.dxf
14.0 x 48.0 mm
