yangit/flactyl/production/manual_3d_print/batch0/Holder v19_wide_0.0_0.5_hole.stl

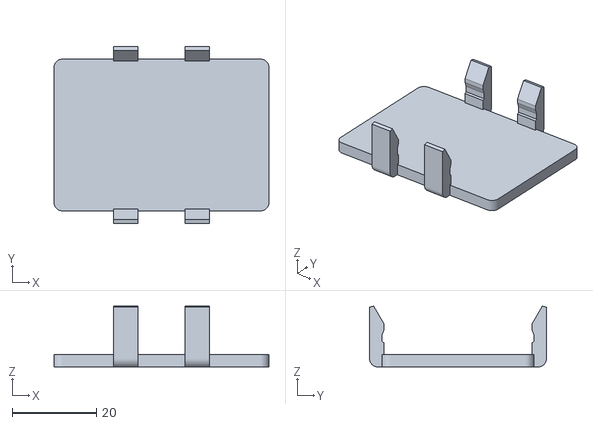
[picture p143: CAD file, 2023-05-24]
production/manual_3d_print/batch0/Holder v19_wide_0.0_0.5_hole.stl
51.0 x 42.0 x 14.4
