yangit/flactyl/production/pcbs/5.1/left/left_switch_cutouts.dxf

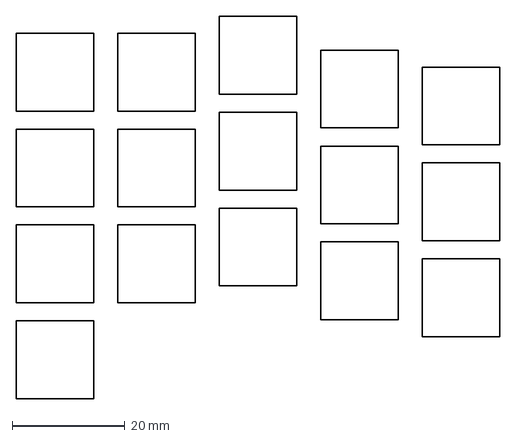
[picture p144: CAD file, 2023-06-08]
production/pcbs/5.1/left/left_switch_cutouts.dxf
85.8 x 67.8 mm
