yangit/flactyl/production/pcbs/5.1/right/right_switch_cutouts.dxf

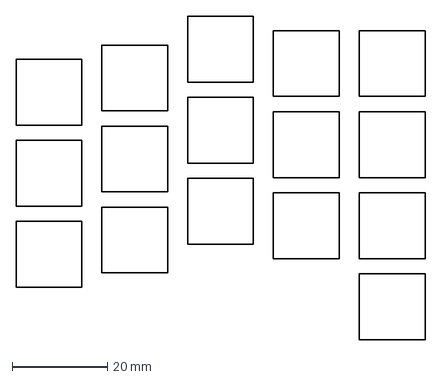
[picture p145: CAD file, 2023-06-08]
production/pcbs/5.1/right/right_switch_cutouts.dxf
85.8 x 67.8 mm
