yangit/flactyl/production/pcbs/5.1/thumb/thumb_pcb_edgecut.dxf

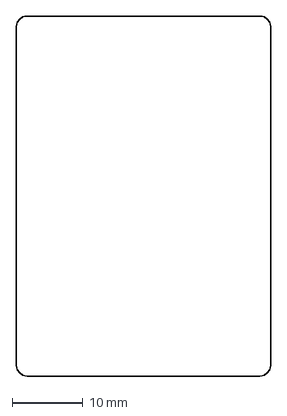
[picture p146: CAD file, 2023-06-01]
production/pcbs/5.1/thumb/thumb_pcb_edgecut.dxf
36.0 x 51.0 mm
