yangit/flactyl/production/pcbs/5.1/thumb3/thumb3_pcb_edgecut.dxf

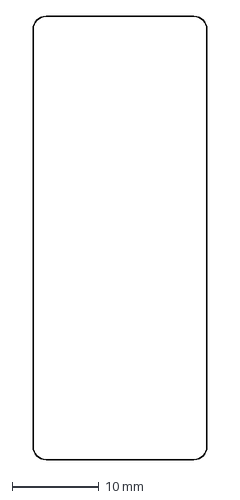
[picture p147: CAD file, 2023-06-29]
production/pcbs/5.1/thumb3/thumb3_pcb_edgecut.dxf
20.0 x 51.0 mm
