yangit/flactyl/production/manual_3d_print/batch0/Holder v27_0.6 edge.stl

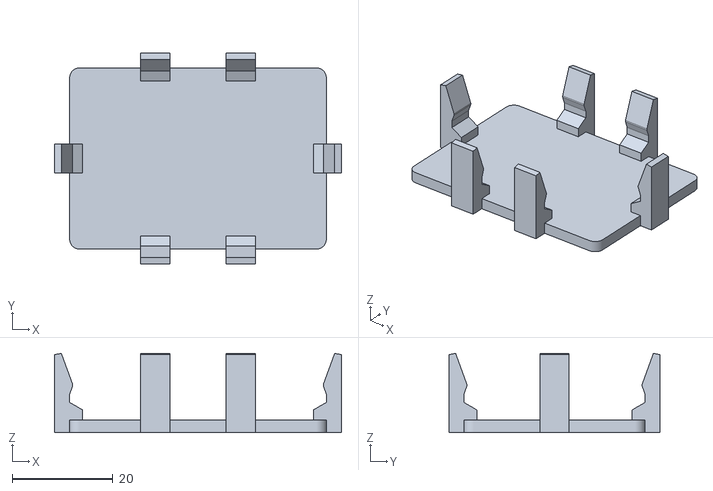
[picture p148: CAD file, 2023-05-24]
production/manual_3d_print/batch0/Holder v27_0.6 edge.stl
57.0 x 42.0 x 15.7
