yangit/flactyl/production/manual_3d_print/batch1/case3 v46.stl

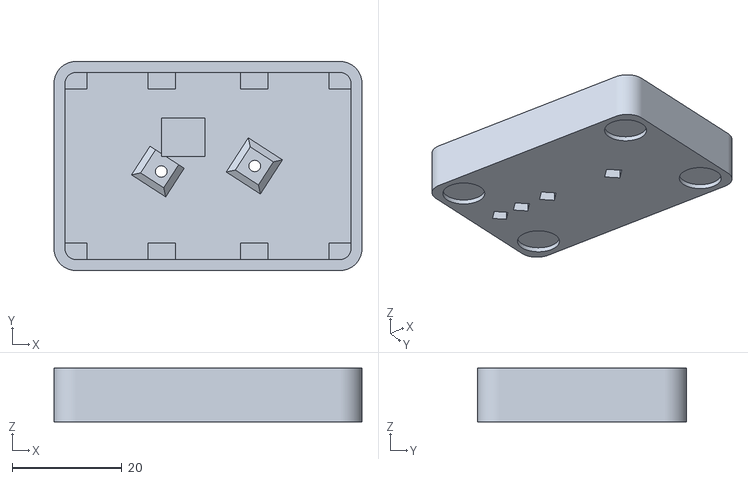
[picture p149: CAD file, 2023-05-24]
production/manual_3d_print/batch1/case3 v46.stl
56.0 x 38.0 x 9.80
