yangit/flactyl/production/pcbs/5.1/right/right_keycaps.dxf

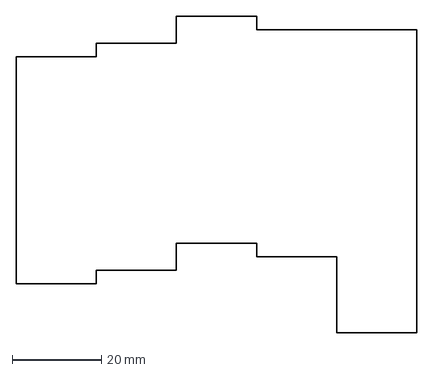
[picture p150: CAD file, 2023-06-08]
production/pcbs/5.1/right/right_keycaps.dxf
90.0 x 71.0 mm
