yangit/flactyl/production/manual_3d_print/batch1/comb.stl

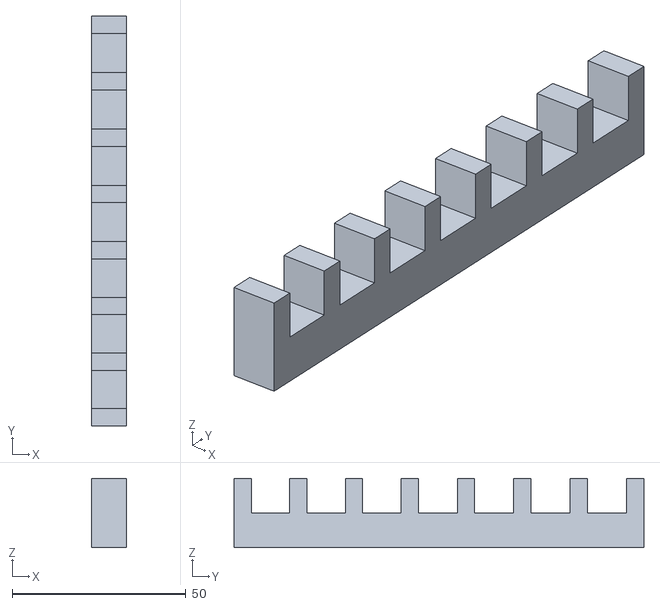
[picture p151: CAD file, 2023-05-24]
production/manual_3d_print/batch1/comb.stl
10.0 x 118.1 x 20.0
