yangit/flactyl/production/pcbs/5.1/left/left_keycaps.dxf

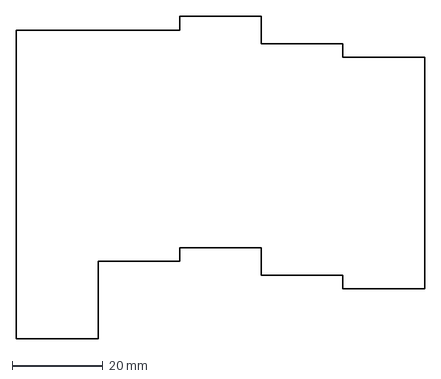
[picture p152: CAD file, 2023-06-08]
production/pcbs/5.1/left/left_keycaps.dxf
90.0 x 71.0 mm
