yangit/flactyl/production/pcbs/5.1/thumb/thumb_config.scad

thumb_keys_xy=[[18,-34,0],[18,-17,0],[18,0,0],[0,-34,180],[0,-17,180],[0,0,180]];
