yangit/flactyl/production/pcbs/5.1/thumb3/thumb3_config.scad

thumb3_keys_xy=[[0,-34,180],[0,-17,0],[0,0,0]];
