yangit/flactyl/scad/hitam/fast.scad

include <./config.scad>;
use <./case.scad>;
use <./lib.scad>;
case ();
