yangit/flactyl/production/pcbs/5.1/test/test_config.scad

test_keys_xy=[[90,-51,180],[90,-34,0]];
