yangit/flactyl/production/4.0/test/test.kicad_pcb

## KiCad design production/4.0/test/test.kicad_pcb (2023-06-08)

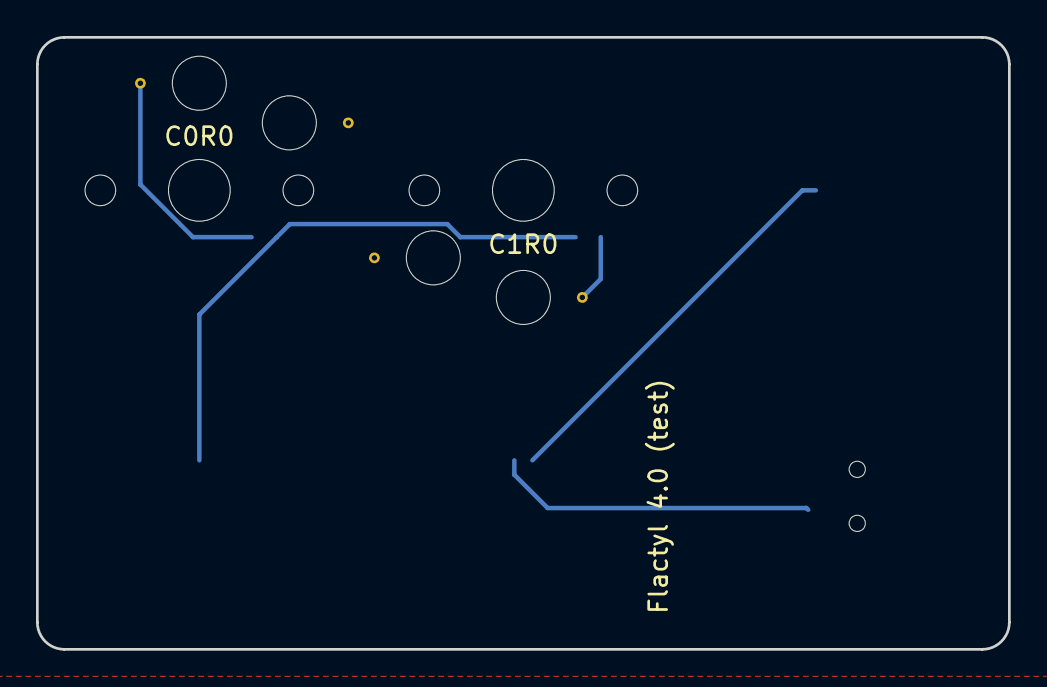
[picture p159: board production/4.0/test/test.kicad_pcb from above]

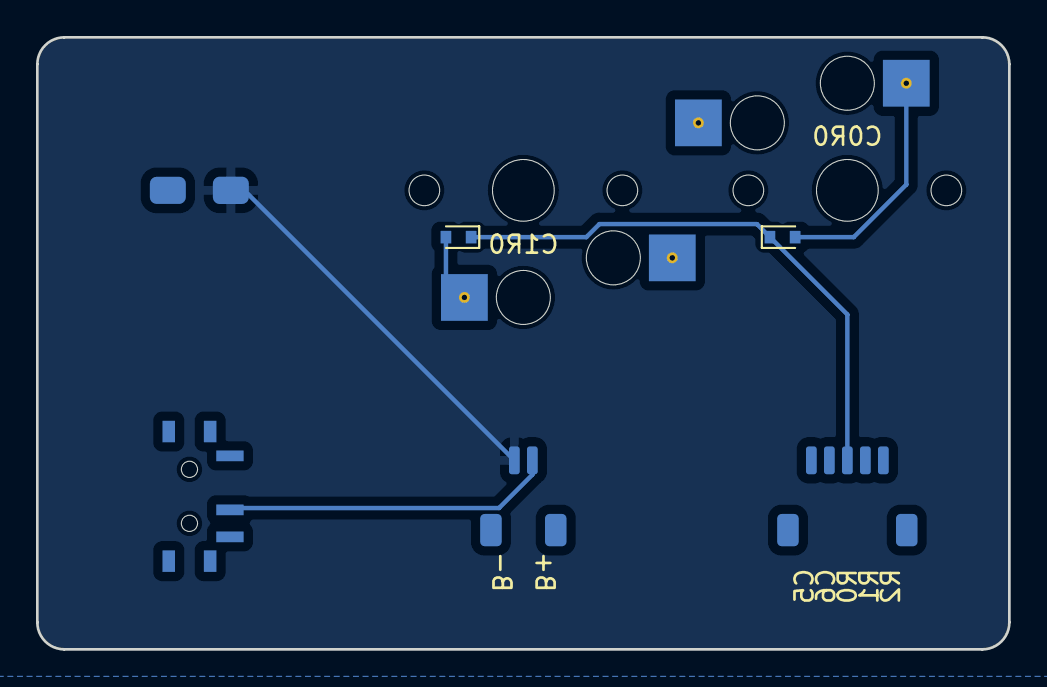
[picture p160: board production/4.0/test/test.kicad_pcb from below]

Board: 2 copper layers, 54.0 x 34.0 mm, 11 parts (7 on the bottom side), 7 nets.

Parts:
D1, D2: D_SOD-523
JB1: JST_SH_SM02B-SRSS-TB_1x02-1MP_P1.00mm_Horizontal
JC1: JST_SH_SM05B-SRSS-TB_1x05-1MP_P1.00mm_Horizontal
S1, S2: Kailh_socket_PG1350_no_silk
SB1: b3u-1000P
SS1: SW-TH_MSK12C02-HB-1
T1: Flactyl 4.0 (test); somelogo
T2: x; somelogo
T3: y; somelogo

Connections:
BSLI: JB1.2, SS1.2
C0: S1.2, S1.4
C0R0D: D1.2, S1.1, S1.3
C1: S2.2, S2.4
C1R0D: D2.2, S2.1, S2.3
GND: JB1.1, SB1.1
R0: D1.1, D2.1, JC1.3
